aGGattack/remoter/project_plan/halo.drawio.png

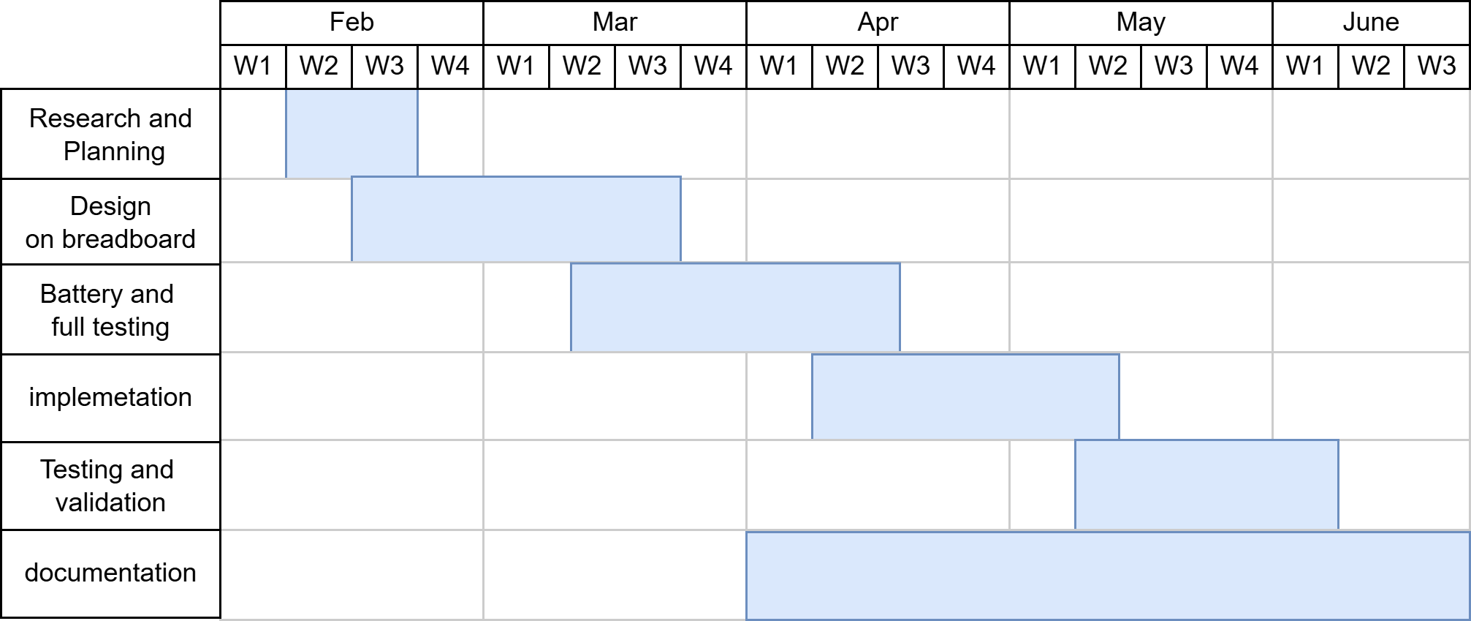
project_plan/halo.drawio.png
