aGGattack/remoter/project_plan/jaja.drawio.png

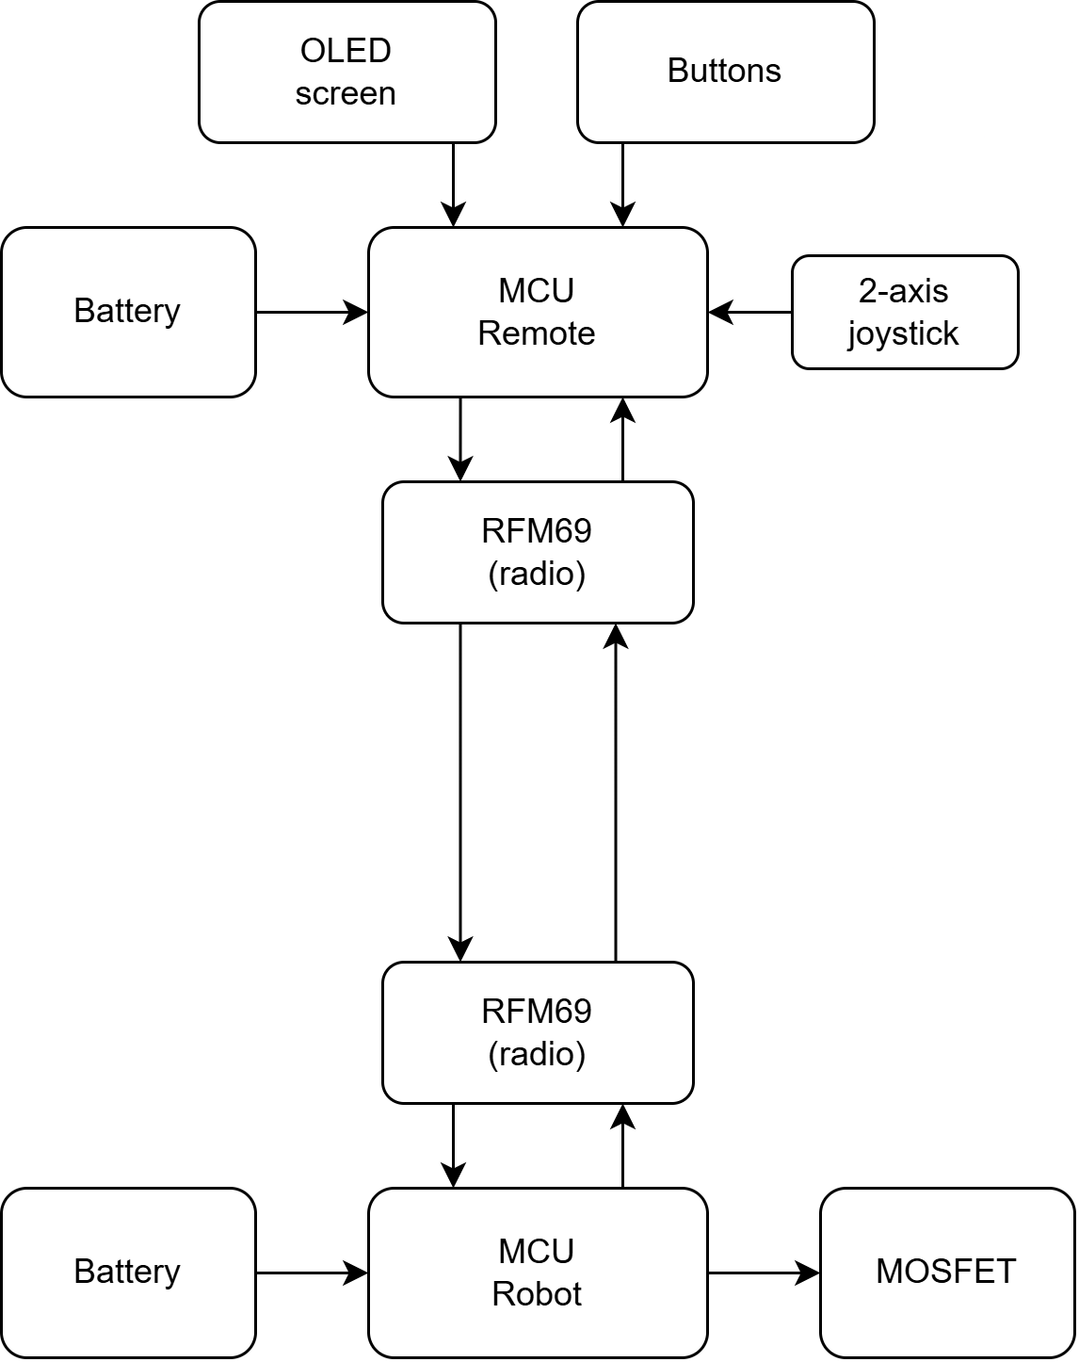
project_plan/jaja.drawio.png
