aGGattack/remoter/project_plan/komnu.drawio.png

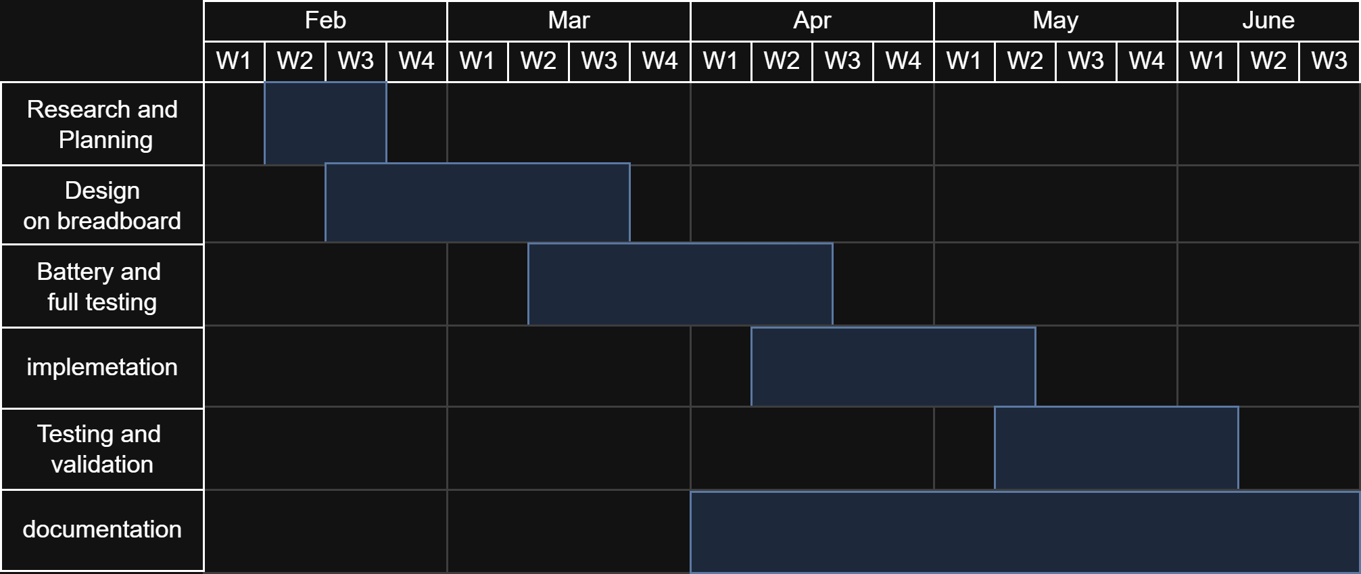
project_plan/komnu.drawio.png
