aGGattack/remoter/project_plan/yeps.drawio.png

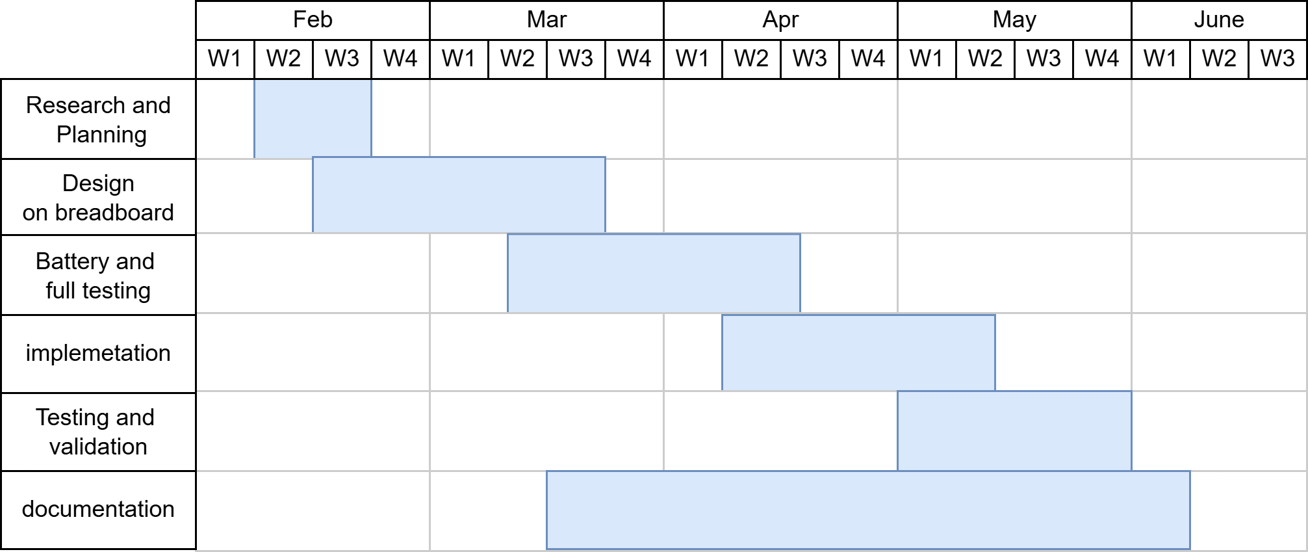
project_plan/yeps.drawio.png
