aGGattack/remoter/Project tests/Latency_Bitrate_PackageSize_Tests/packet_size_5B_9.6kb20260520_161618.png

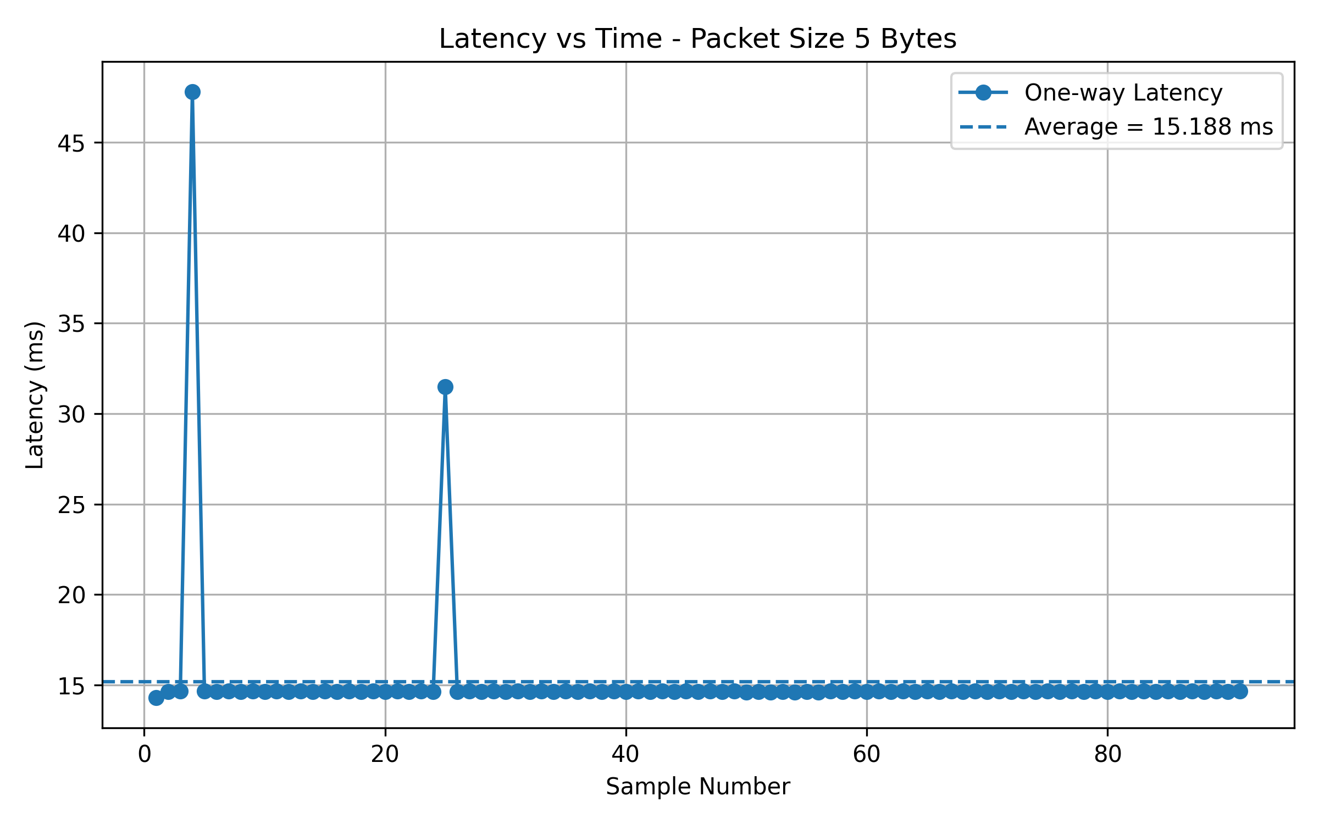
Project tests/Latency_Bitrate_PackageSize_Tests/packet_size_5B_9.6kb20260520_161618.png
