aGGattack/remoter/Project tests/Latency_Bitrate_PackageSize_Tests/packet_size_5B_57.6kb20260520_161243.png

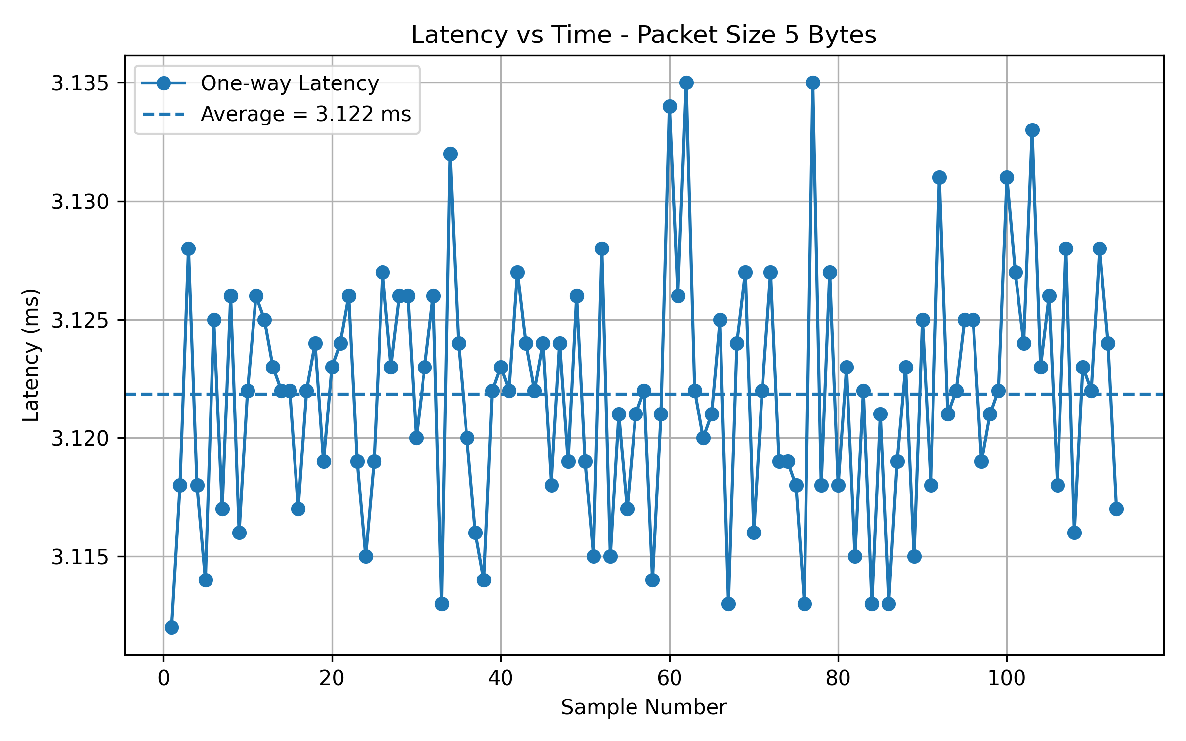
Project tests/Latency_Bitrate_PackageSize_Tests/packet_size_5B_57.6kb20260520_161243.png
