aGGattack/remoter/Project tests/Latency_Bitrate_PackageSize_Tests/packet_size_5B_115.2kb20260520_162811.png

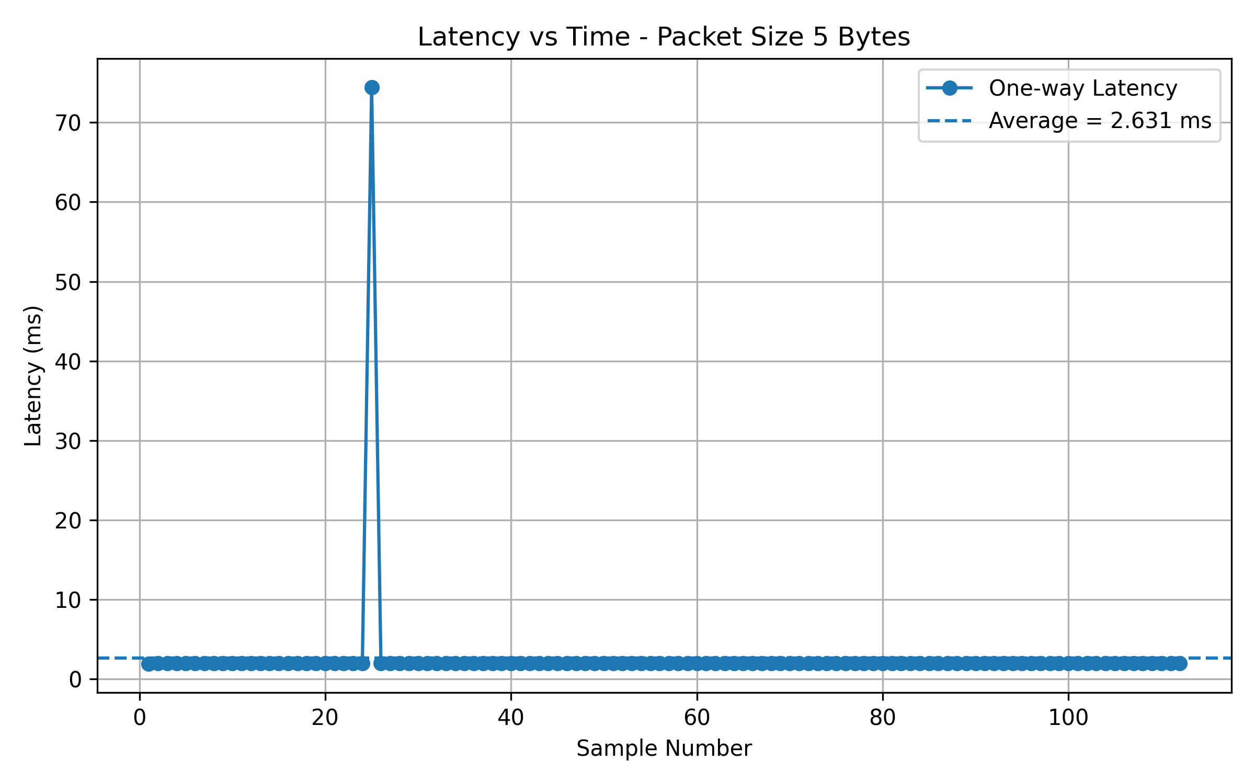
Project tests/Latency_Bitrate_PackageSize_Tests/packet_size_5B_115.2kb20260520_162811.png
