aGGattack/remoter/Project tests/Latency_Bitrate_PackageSize_Tests/packet_size_16B_9.6kb20260520_161730.png

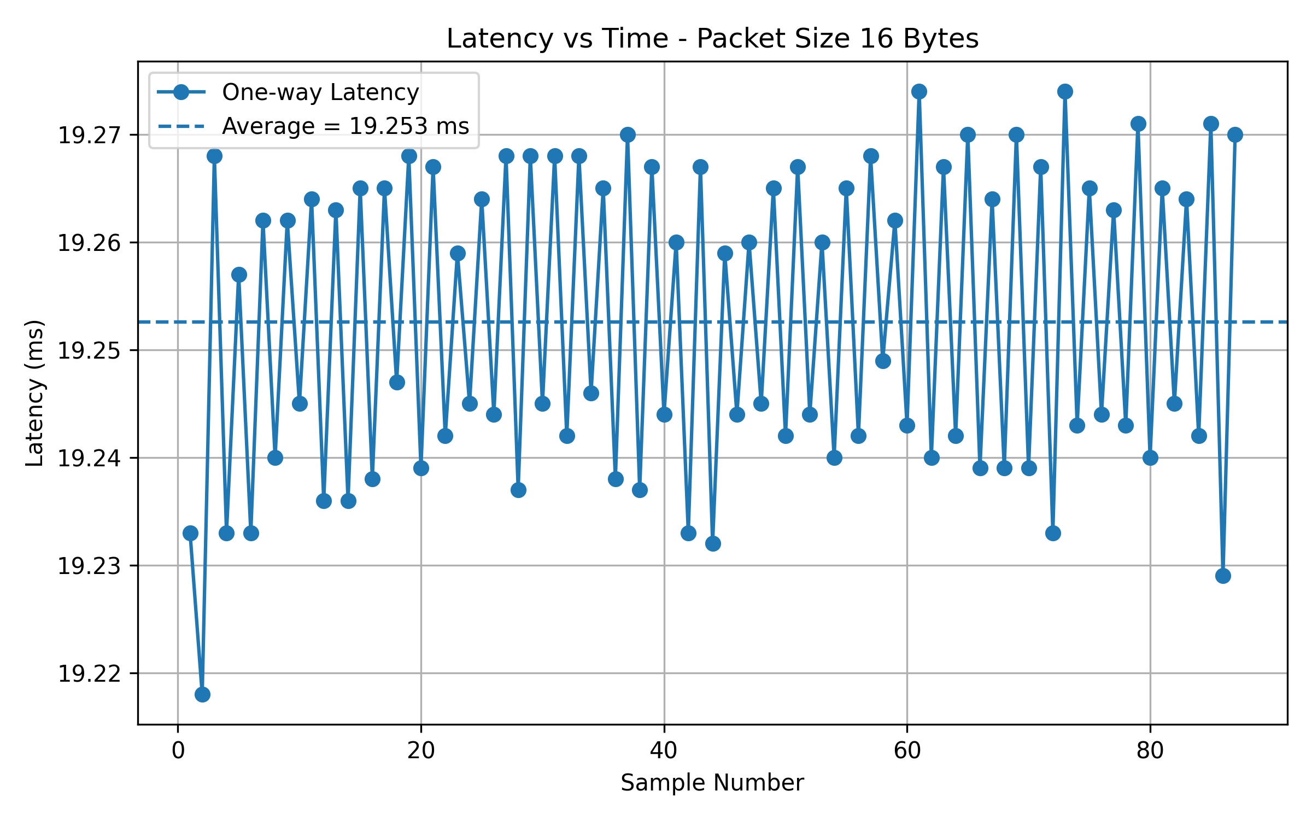
Project tests/Latency_Bitrate_PackageSize_Tests/packet_size_16B_9.6kb20260520_161730.png
