aGGattack/remoter/Project tests/Latency_Bitrate_PackageSize_Tests/packet_size_16B_57.6kb20260520_161135.png

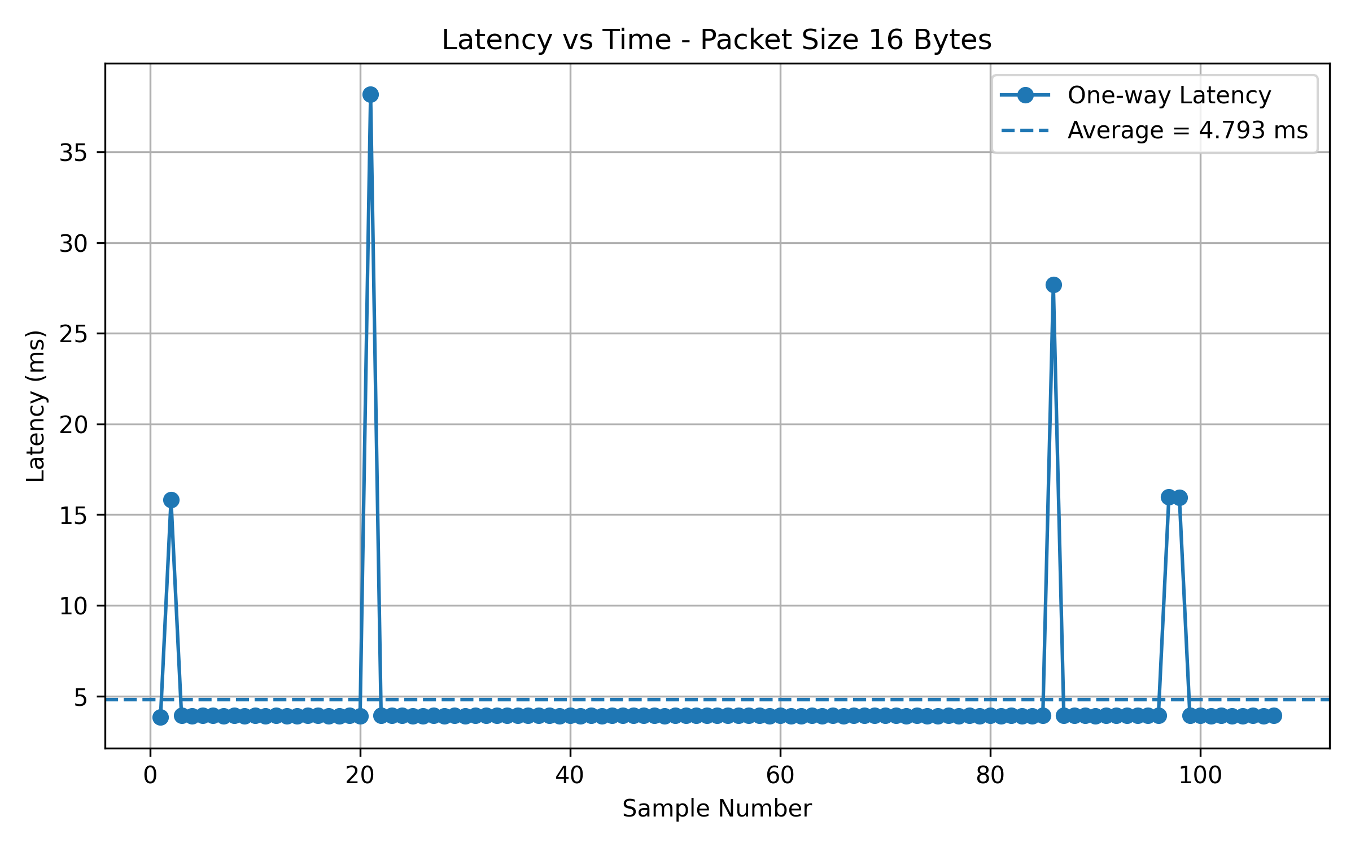
Project tests/Latency_Bitrate_PackageSize_Tests/packet_size_16B_57.6kb20260520_161135.png
