aGGattack/remoter/Project tests/Latency_Bitrate_PackageSize_Tests/packet_size_16B_115.2kb20260520_162728.png

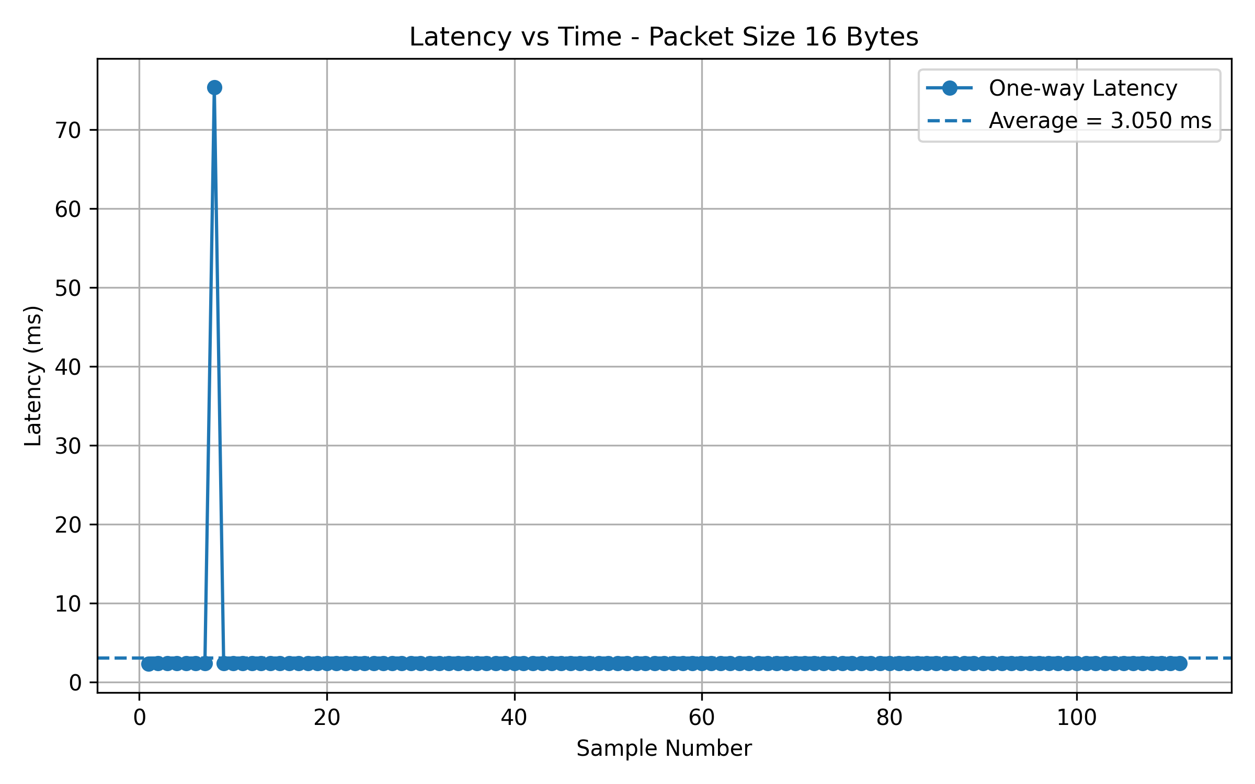
Project tests/Latency_Bitrate_PackageSize_Tests/packet_size_16B_115.2kb20260520_162728.png
