aGGattack/remoter/Project tests/Latency_Bitrate_PackageSize_Tests/packet_size_32B_9.6kb20260520_161826.png

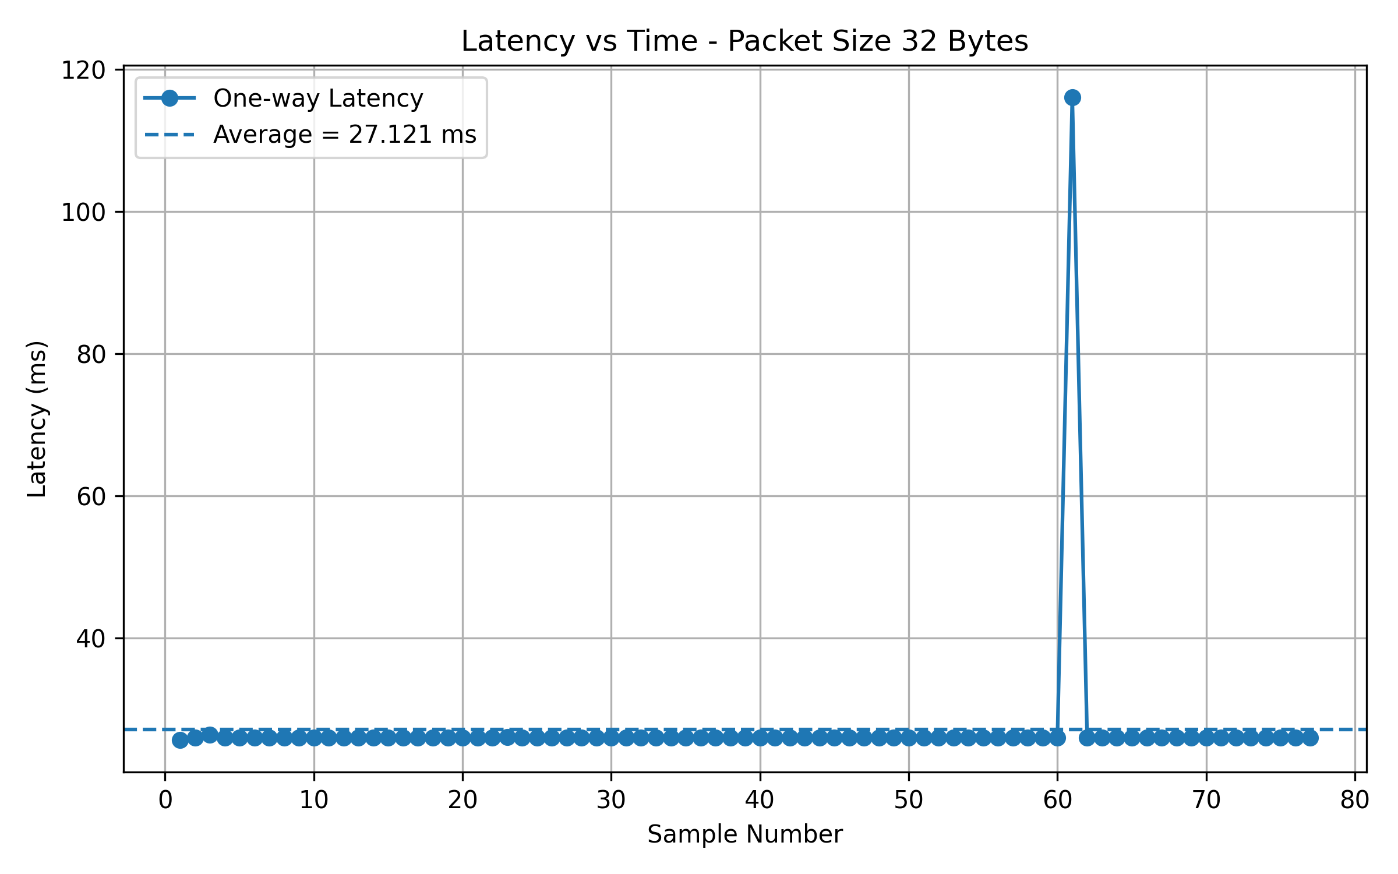
Project tests/Latency_Bitrate_PackageSize_Tests/packet_size_32B_9.6kb20260520_161826.png
