aGGattack/remoter/Project tests/Latency_Bitrate_PackageSize_Tests/packet_size_32B_57.6kb20260520_161049.png

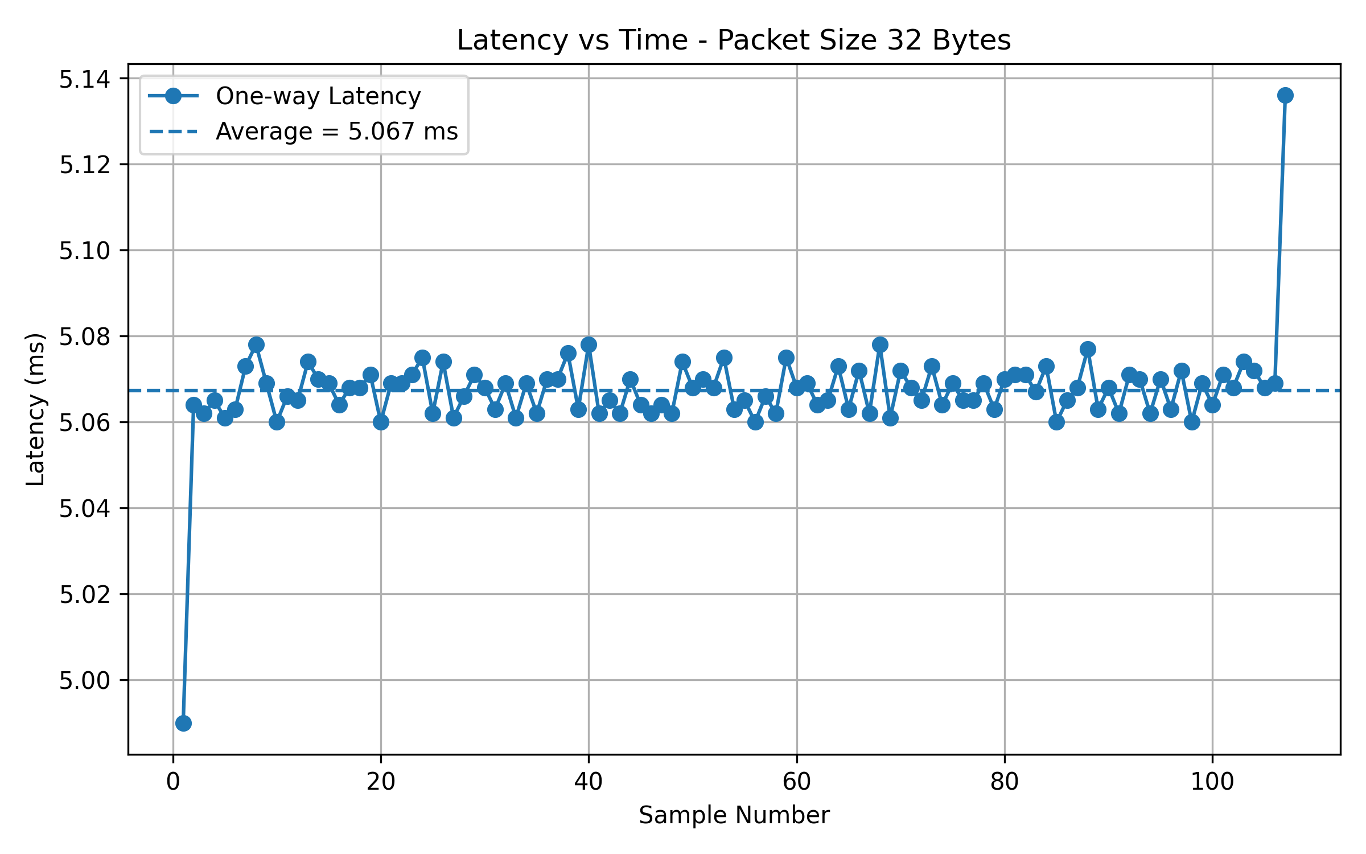
Project tests/Latency_Bitrate_PackageSize_Tests/packet_size_32B_57.6kb20260520_161049.png
