aGGattack/remoter/Project tests/Latency_Bitrate_PackageSize_Tests/packet_size_32B_115.2kb20260520_162636.png

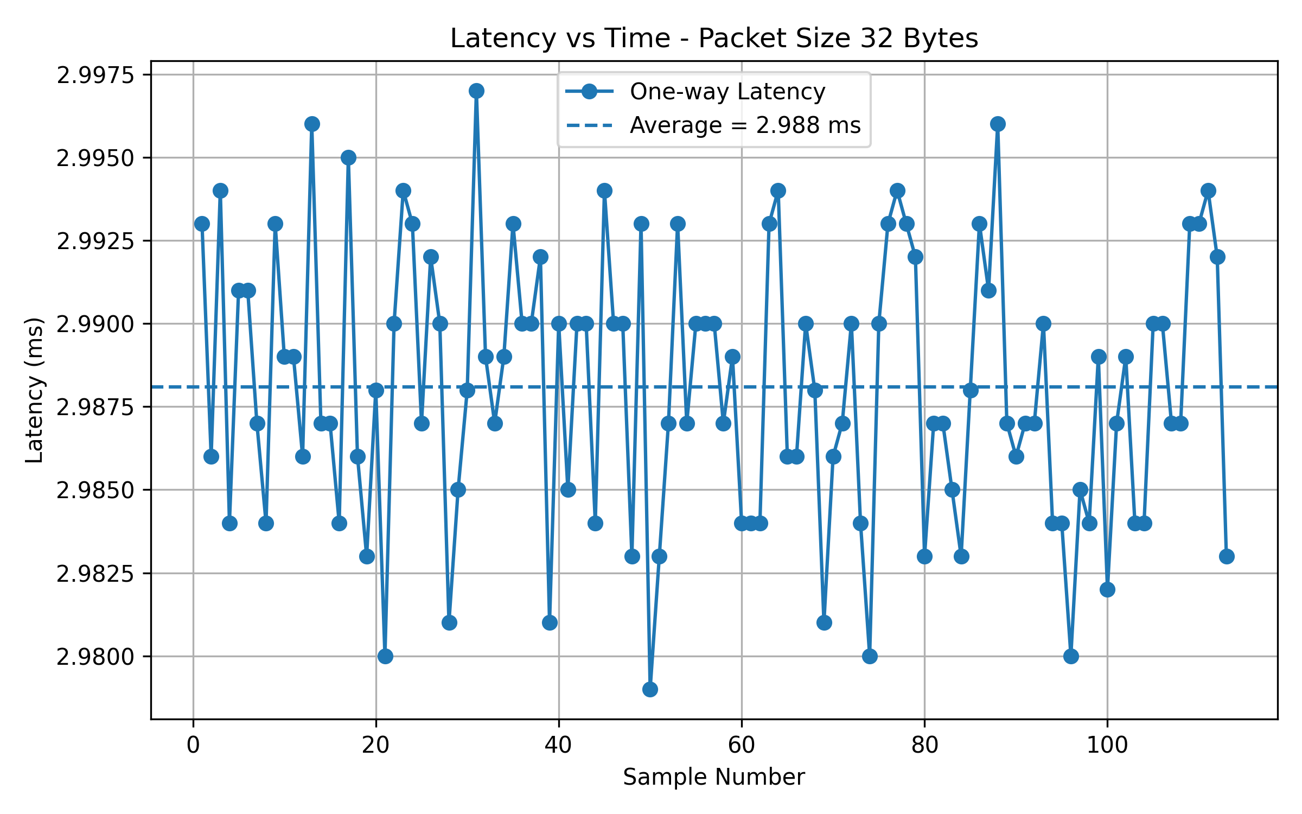
Project tests/Latency_Bitrate_PackageSize_Tests/packet_size_32B_115.2kb20260520_162636.png
