aGGattack/remoter/Project tests/Latency_Bitrate_PackageSize_Tests/packet_size_48B_9.6kb20260520_162034.png

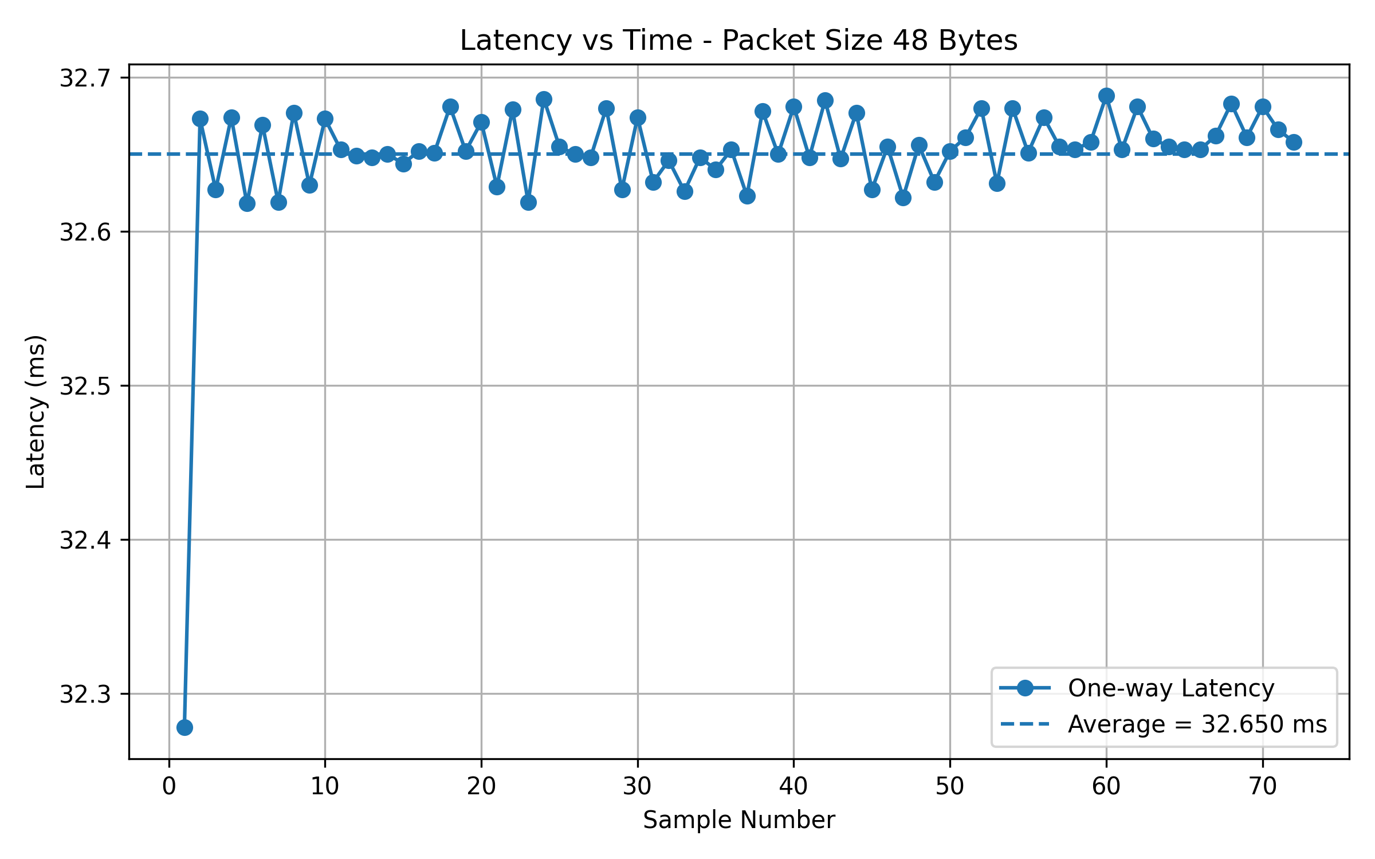
Project tests/Latency_Bitrate_PackageSize_Tests/packet_size_48B_9.6kb20260520_162034.png
