aGGattack/remoter/Project tests/Latency_Bitrate_PackageSize_Tests/packet_size_48B_57.6kb20260520_161003.png

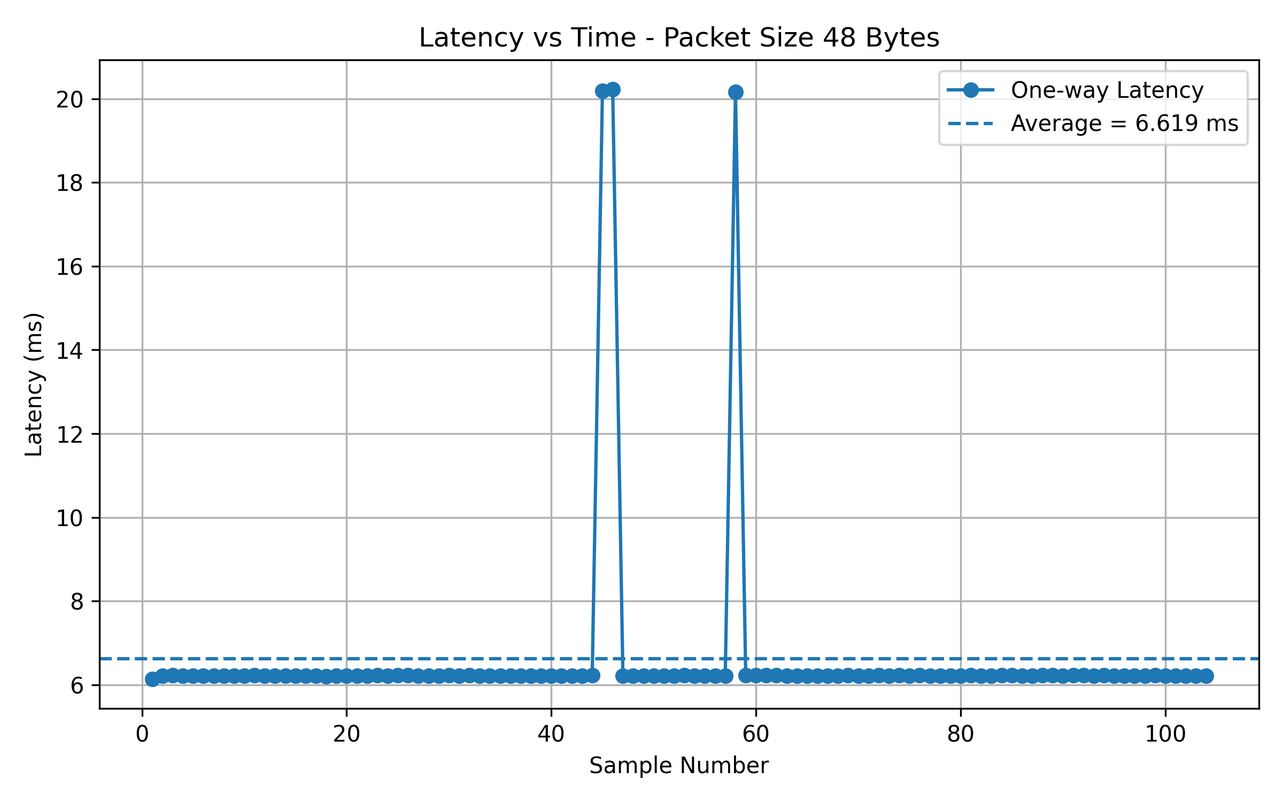
Project tests/Latency_Bitrate_PackageSize_Tests/packet_size_48B_57.6kb20260520_161003.png
