aGGattack/remoter/Project tests/Latency_Bitrate_PackageSize_Tests/packet_size_48B_115.2kb20260520_162426.png

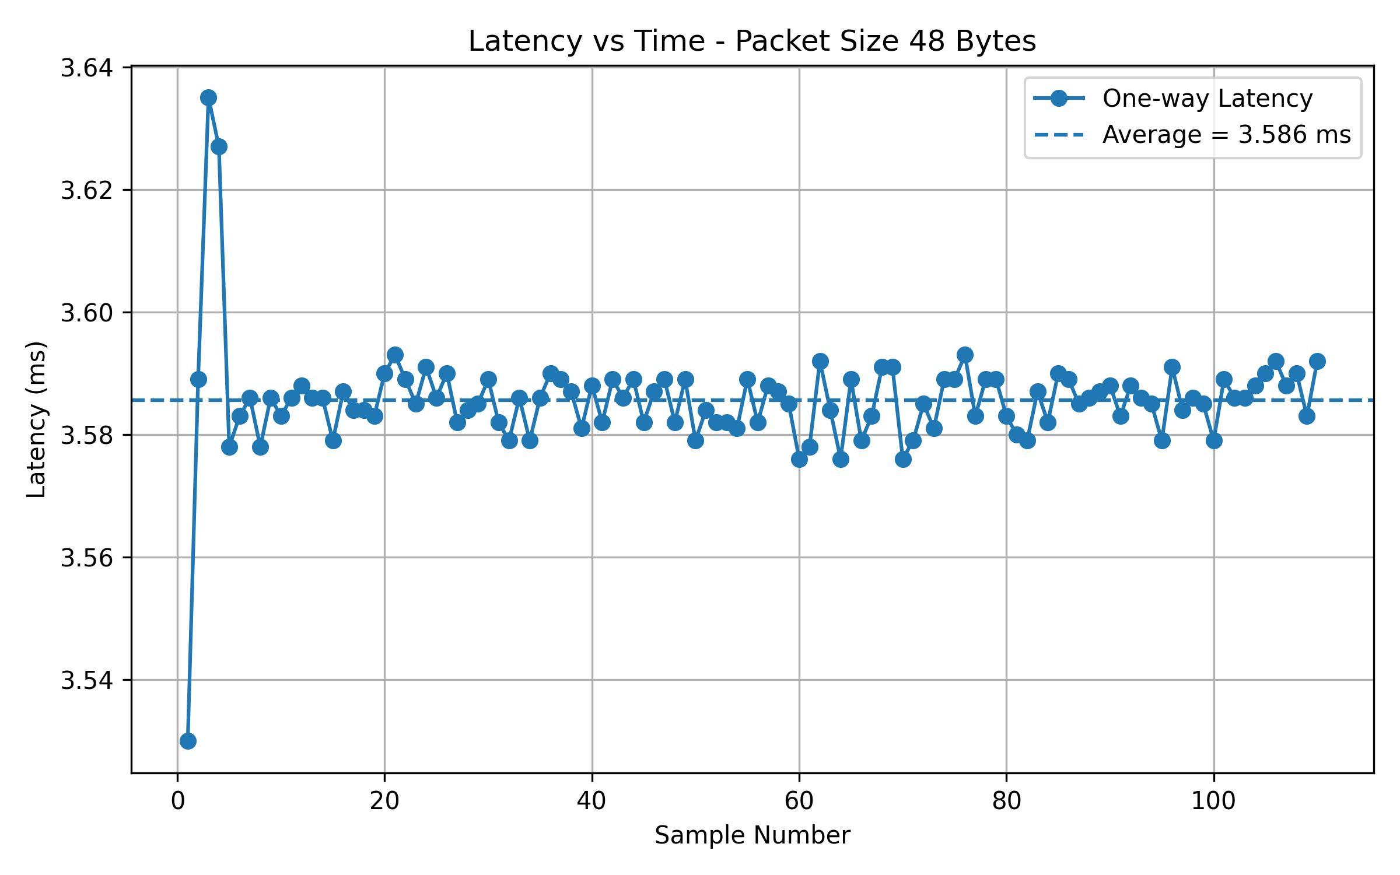
Project tests/Latency_Bitrate_PackageSize_Tests/packet_size_48B_115.2kb20260520_162426.png
