aGGattack/remoter/Project tests/Latency_Bitrate_PackageSize_Tests/packet_size_64B_9.6kb20260520_162110.png

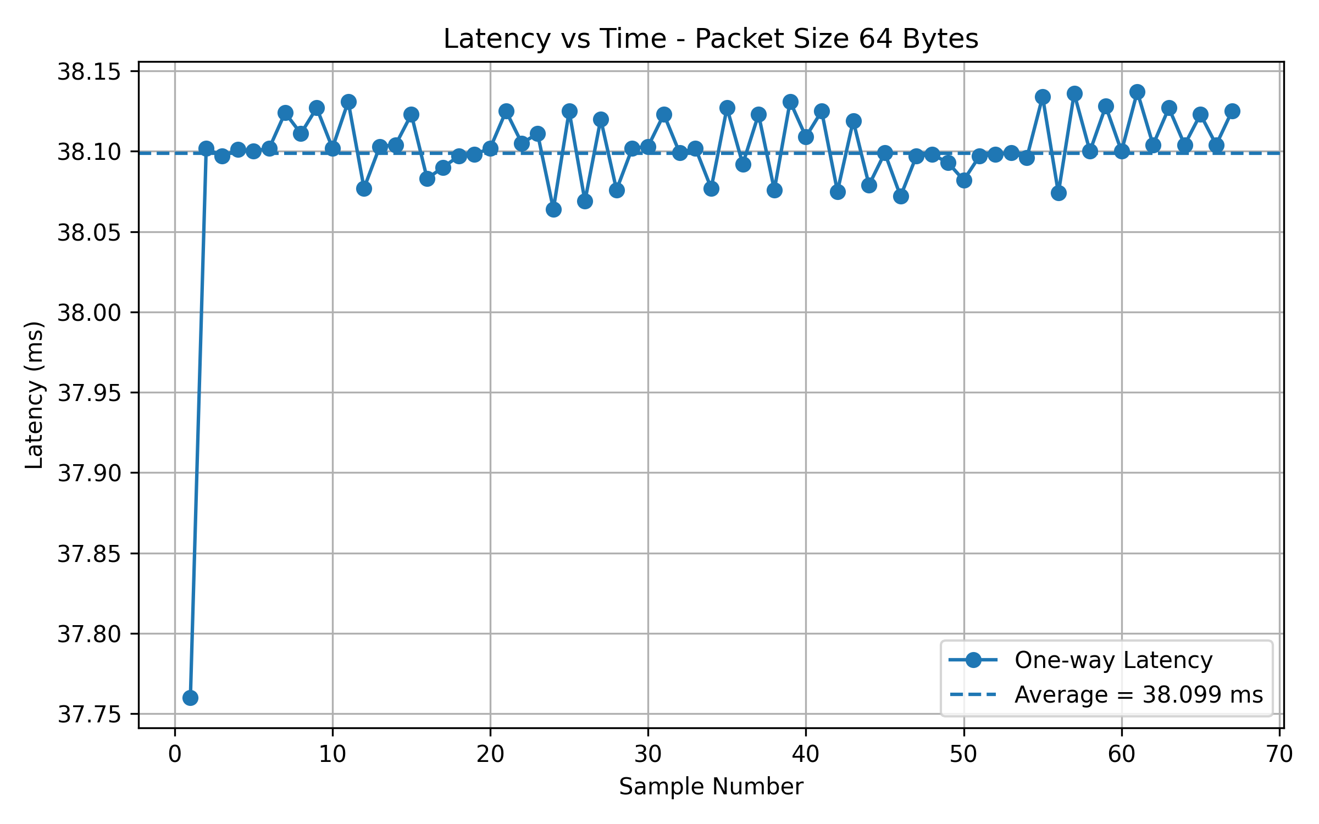
Project tests/Latency_Bitrate_PackageSize_Tests/packet_size_64B_9.6kb20260520_162110.png
