aGGattack/remoter/Project tests/Latency_Bitrate_PackageSize_Tests/plot_boxplot_rtt.png

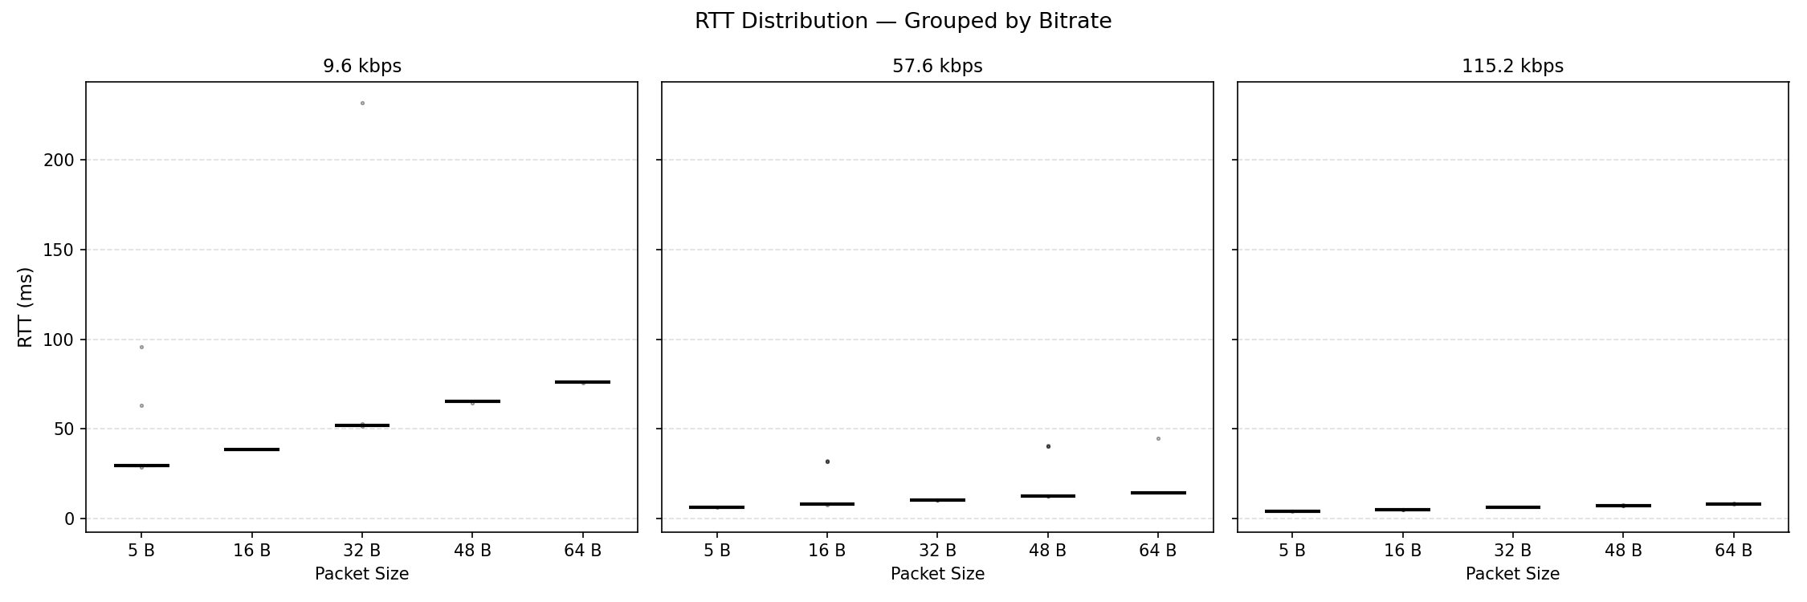
Project tests/Latency_Bitrate_PackageSize_Tests/plot_boxplot_rtt.png
