aGGattack/remoter/Project tests/Latency_Bitrate_PackageSize_Tests/plot_grouped_bar.png

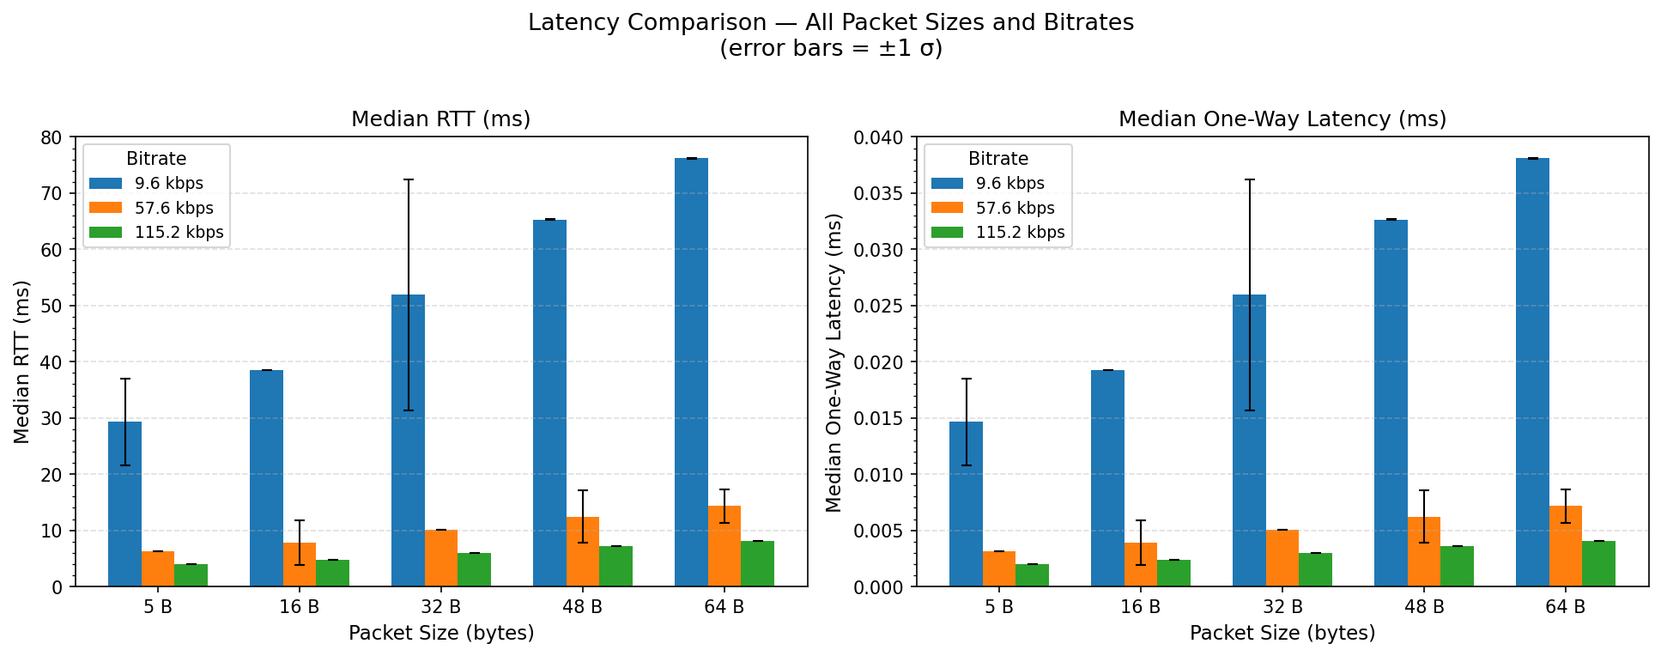
Project tests/Latency_Bitrate_PackageSize_Tests/plot_grouped_bar.png
