aGGattack/remoter/Project tests/Latency_Bitrate_PackageSize_Tests/plot_heatmap_owl.png

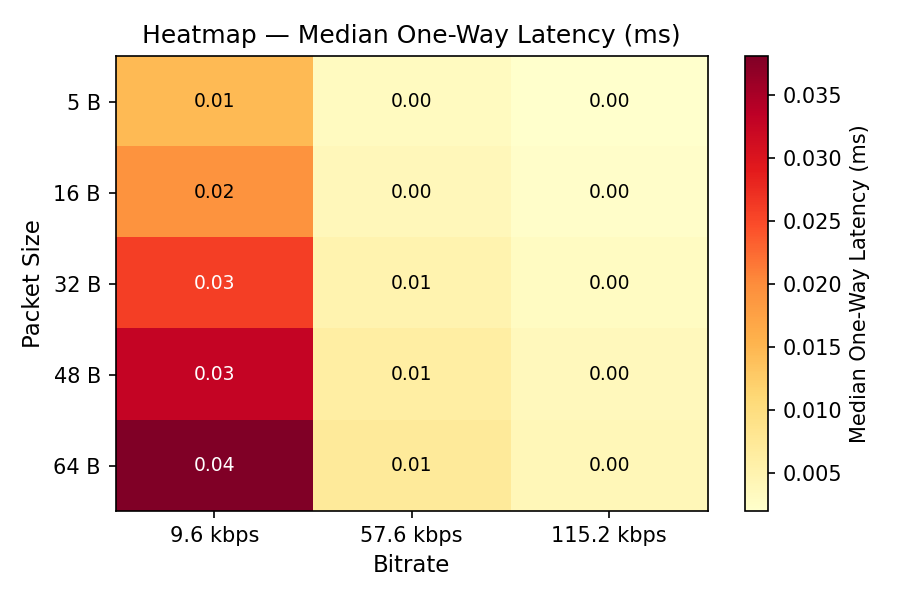
Project tests/Latency_Bitrate_PackageSize_Tests/plot_heatmap_owl.png
