aGGattack/remoter/Project tests/Latency_Bitrate_PackageSize_Tests/plot_owl_vs_packet_size.png

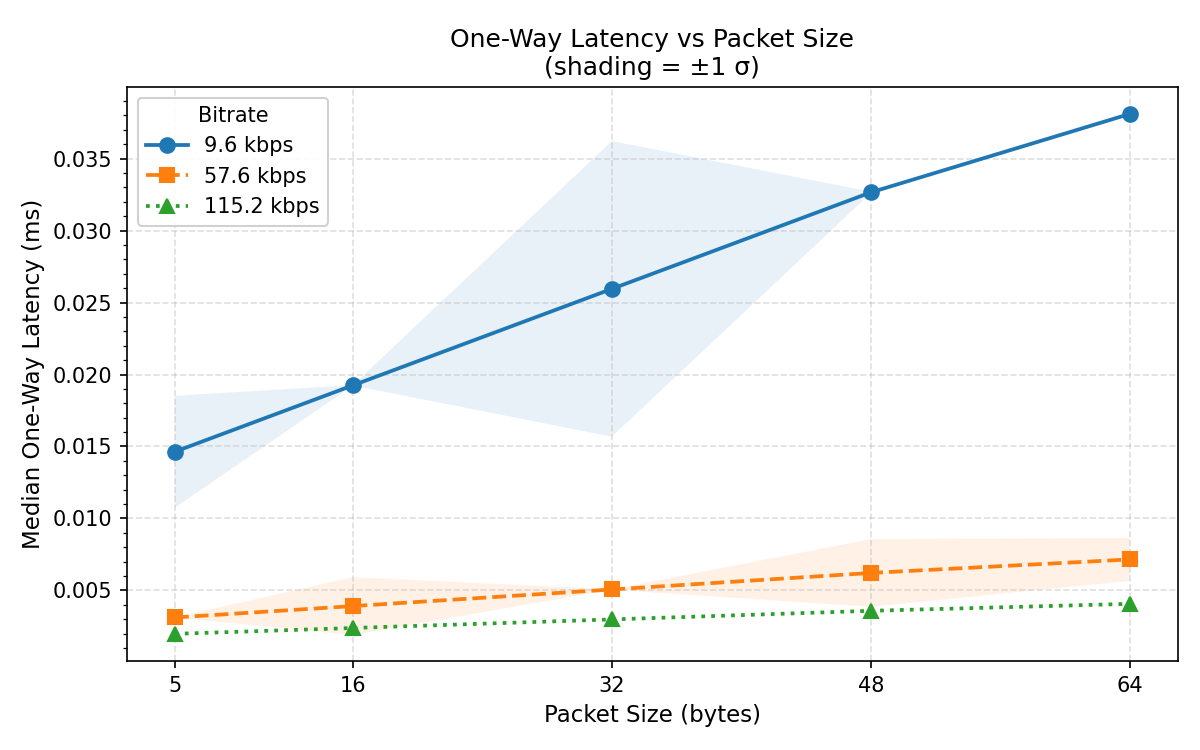
Project tests/Latency_Bitrate_PackageSize_Tests/plot_owl_vs_packet_size.png
