aGGattack/remoter/Project tests/latency_Bitrate_test/latency_1.2_kbps_20260520_152502.png

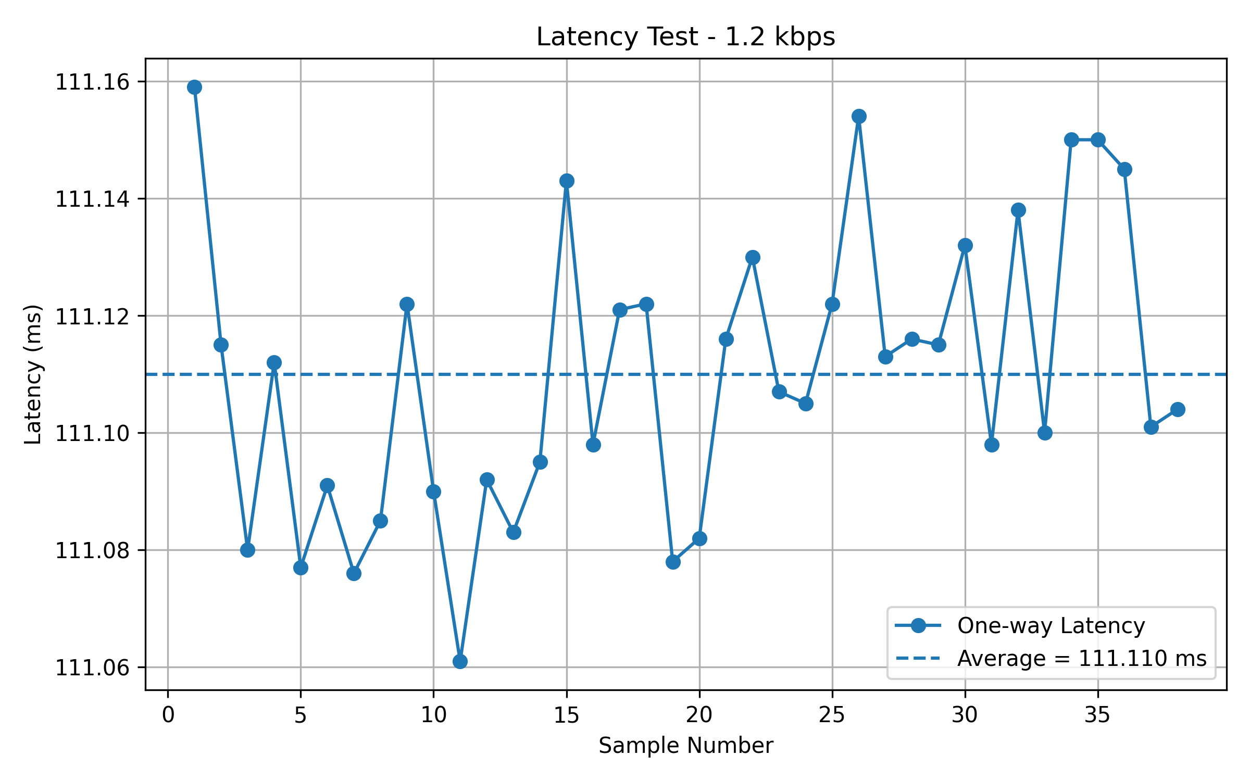
Project tests/latency_Bitrate_test/latency_1.2_kbps_20260520_152502.png
