aGGattack/remoter/Project tests/latency_Bitrate_test/latency_9.6_kbps_20260520_150811.png

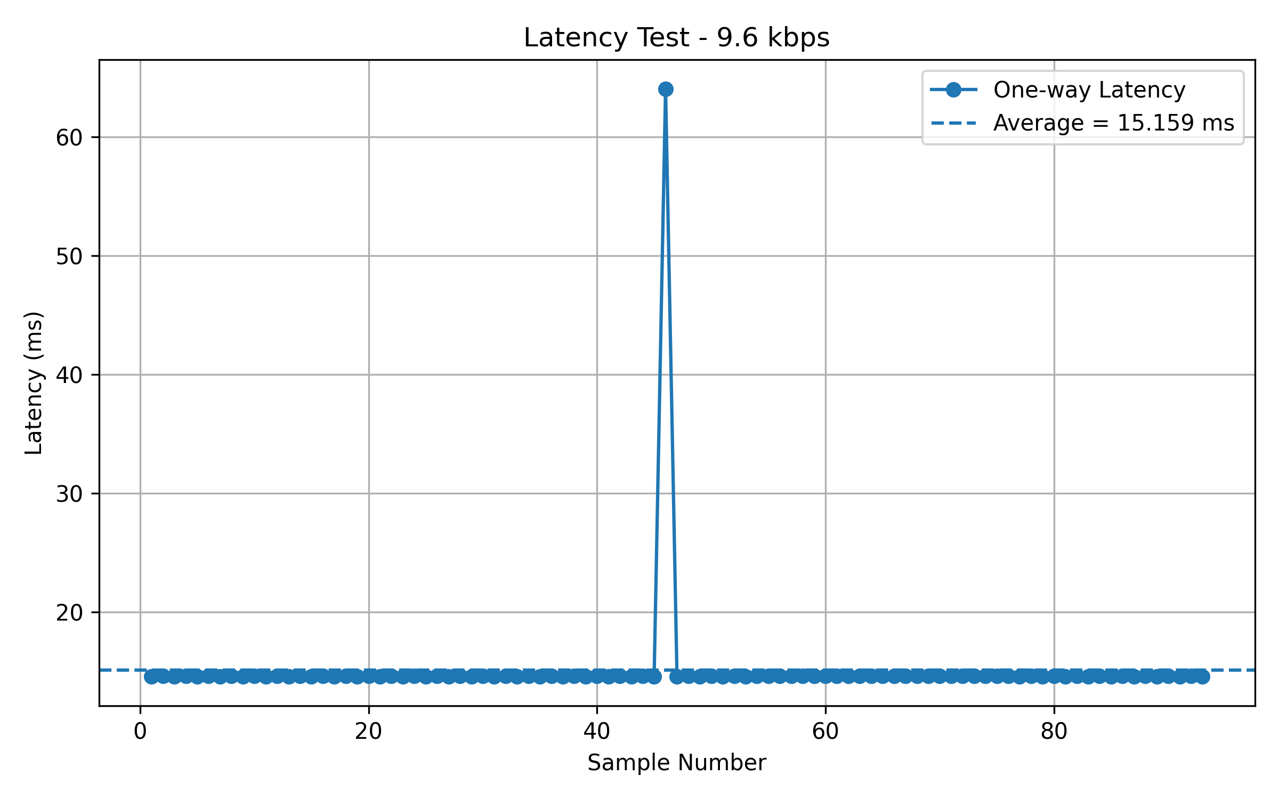
Project tests/latency_Bitrate_test/latency_9.6_kbps_20260520_150811.png
