aGGattack/remoter/Project tests/latency_Bitrate_test/latency_57.6_kbps_20260520_150318.png

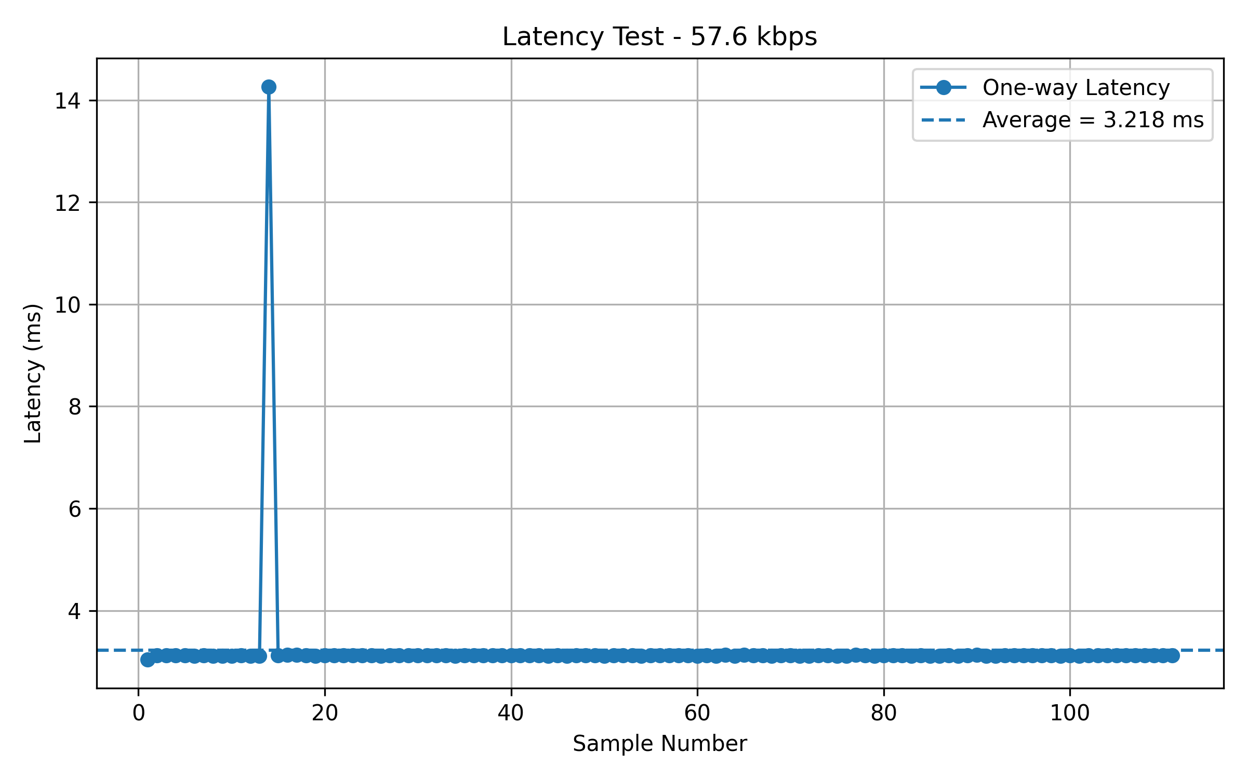
Project tests/latency_Bitrate_test/latency_57.6_kbps_20260520_150318.png
