aGGattack/remoter/Project tests/latency_Bitrate_test/latency_115.2_kbps_20260520_150950.png

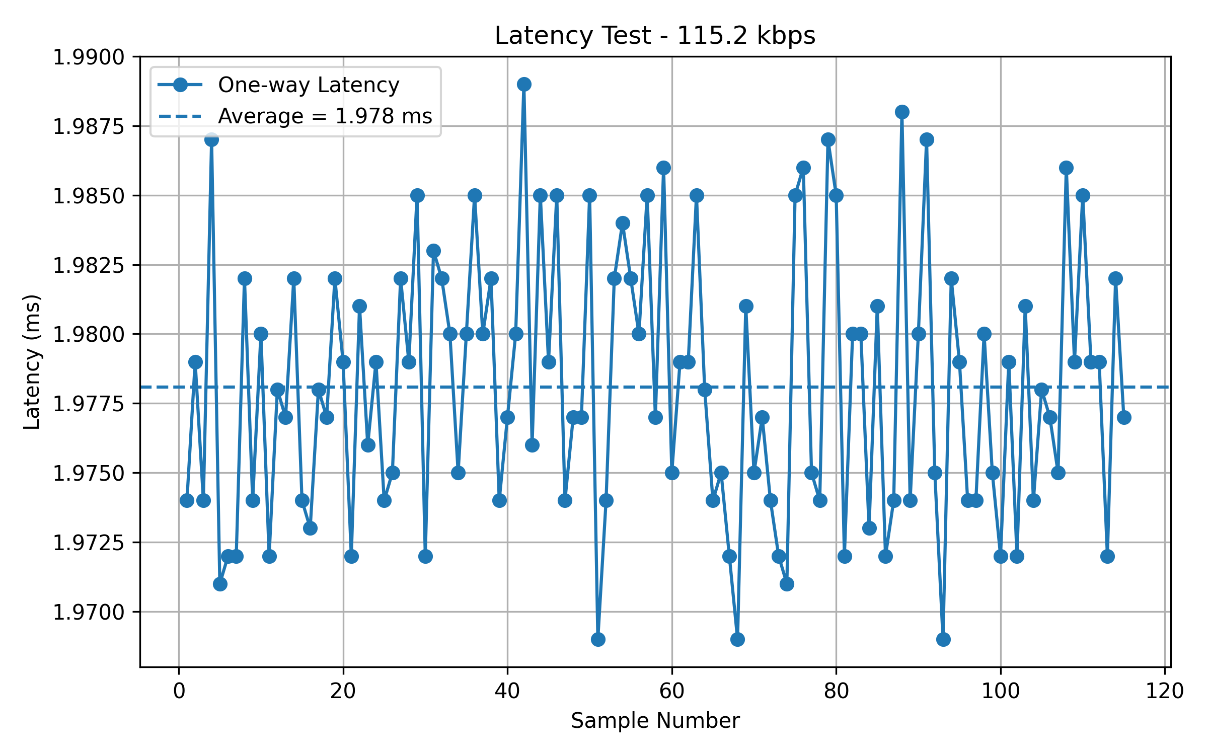
Project tests/latency_Bitrate_test/latency_115.2_kbps_20260520_150950.png
