aGGattack/remoter/Project tests/latency_Bitrate_test/latency_250_kbps_20260520_151310.png

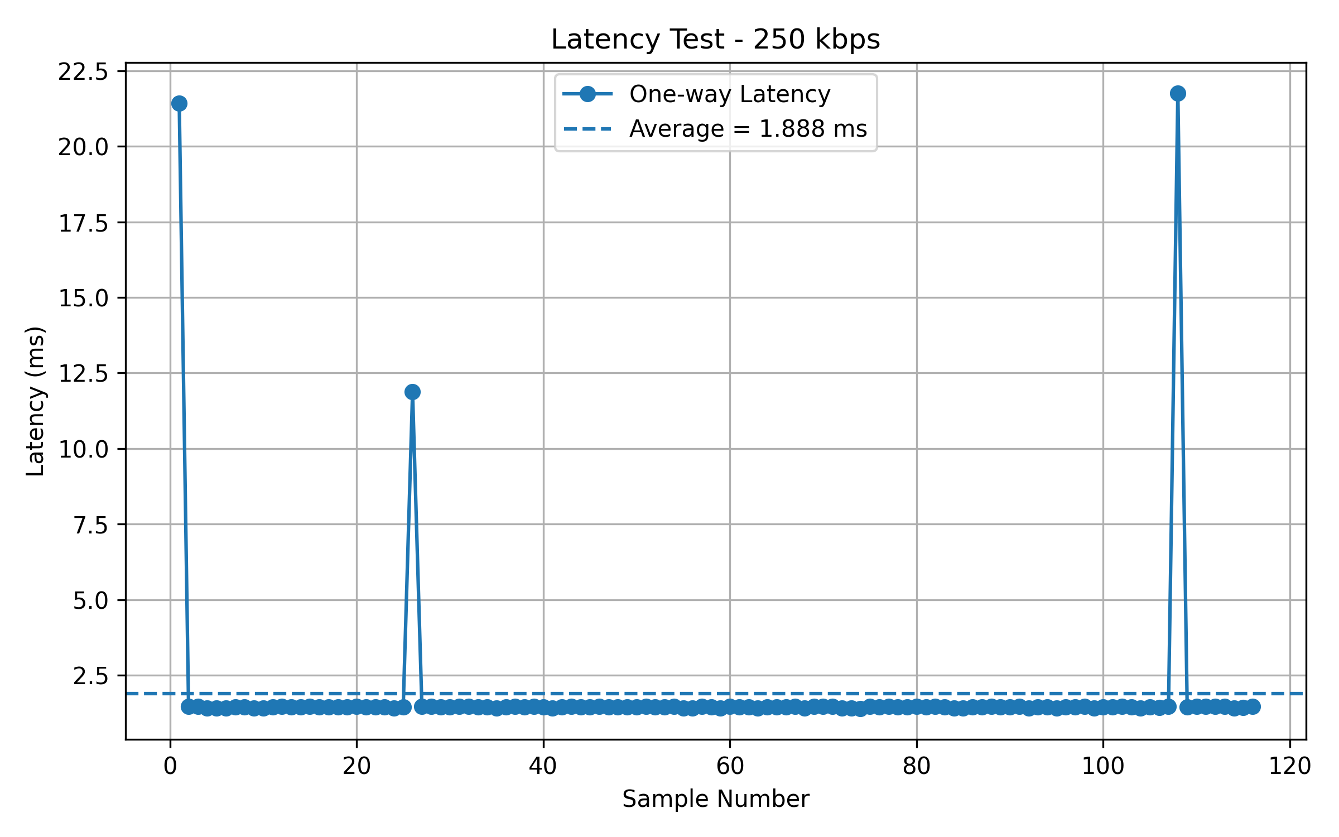
Project tests/latency_Bitrate_test/latency_250_kbps_20260520_151310.png
