aGGattack/remoter/Project tests/latency_Bitrate_test/plot_bar_rtt_owl.png

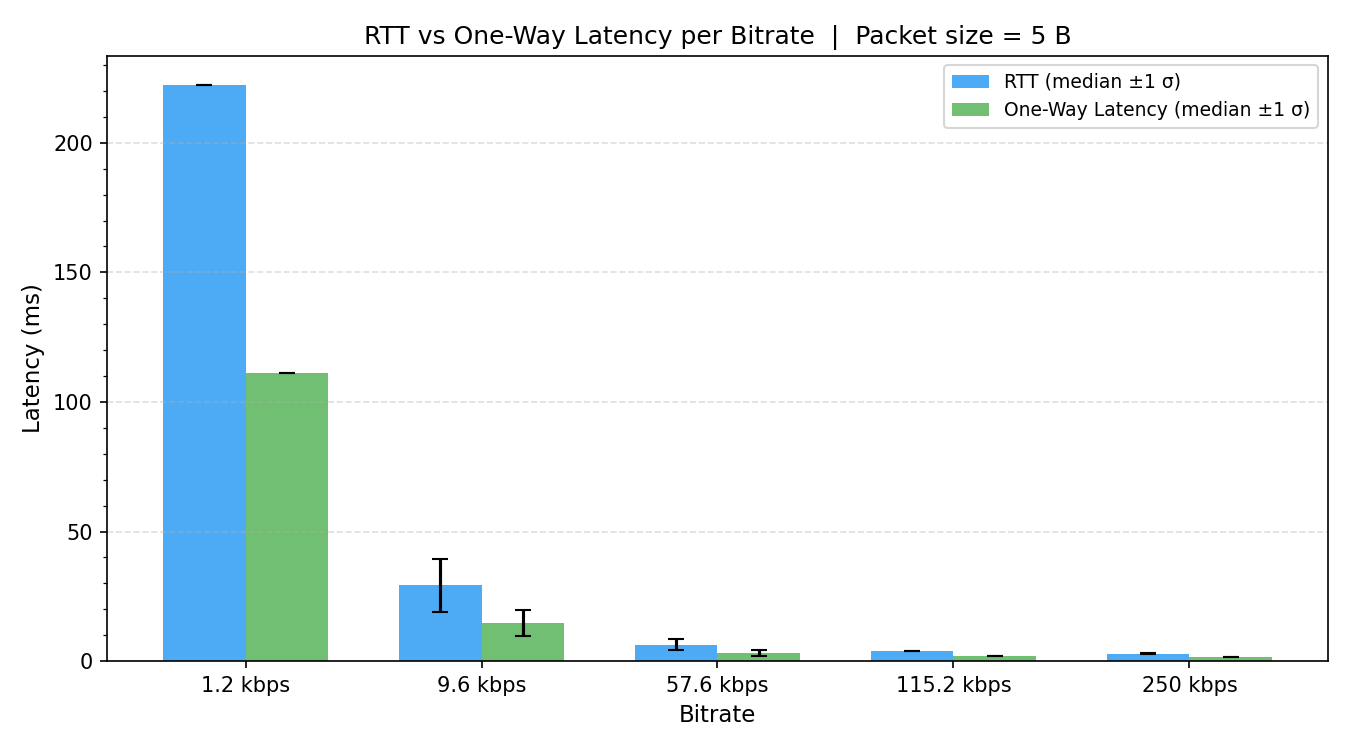
Project tests/latency_Bitrate_test/plot_bar_rtt_owl.png
