aGGattack/remoter/Project tests/latency_Bitrate_test/plot_boxplot_bitrate.png

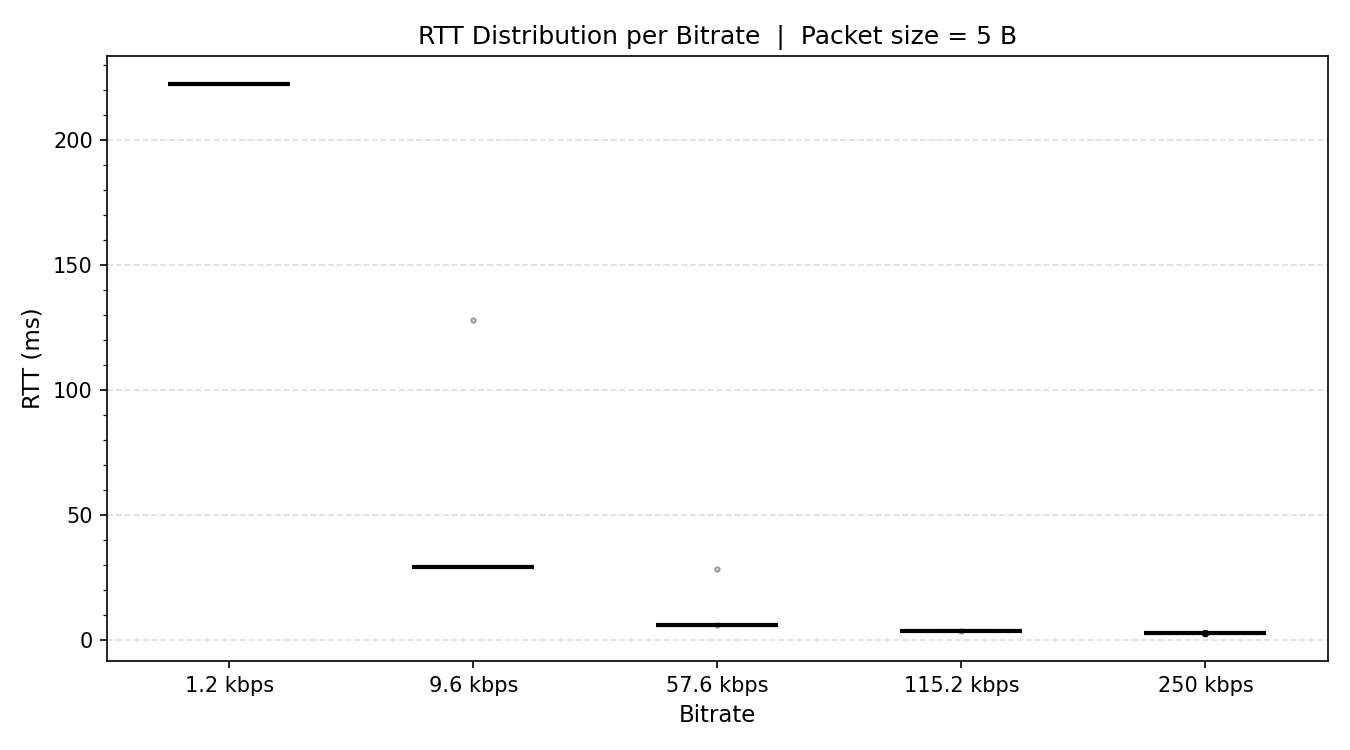
Project tests/latency_Bitrate_test/plot_boxplot_bitrate.png
