aGGattack/remoter/Project tests/latency_Bitrate_test/plot_rtt_vs_bitrate.png

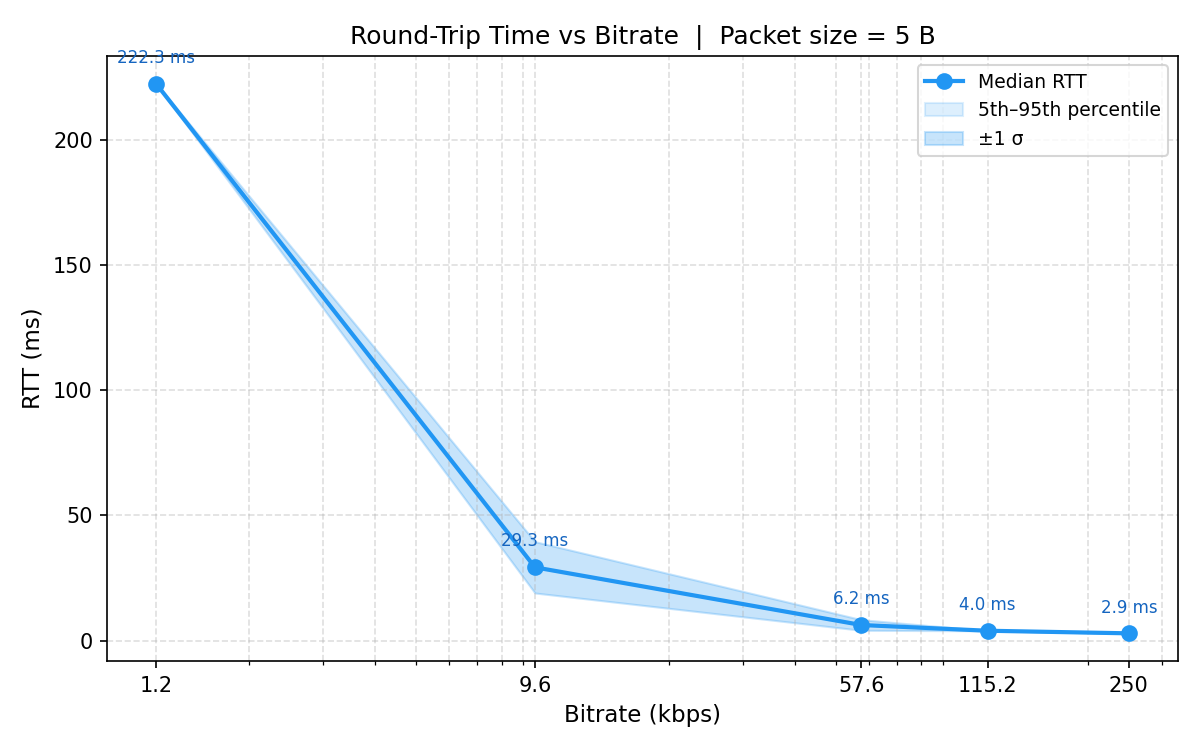
Project tests/latency_Bitrate_test/plot_rtt_vs_bitrate.png
