aGGattack/remoter/Project tests/RSSI_Antenna_test/plot_rssi_bar_per_distance.png

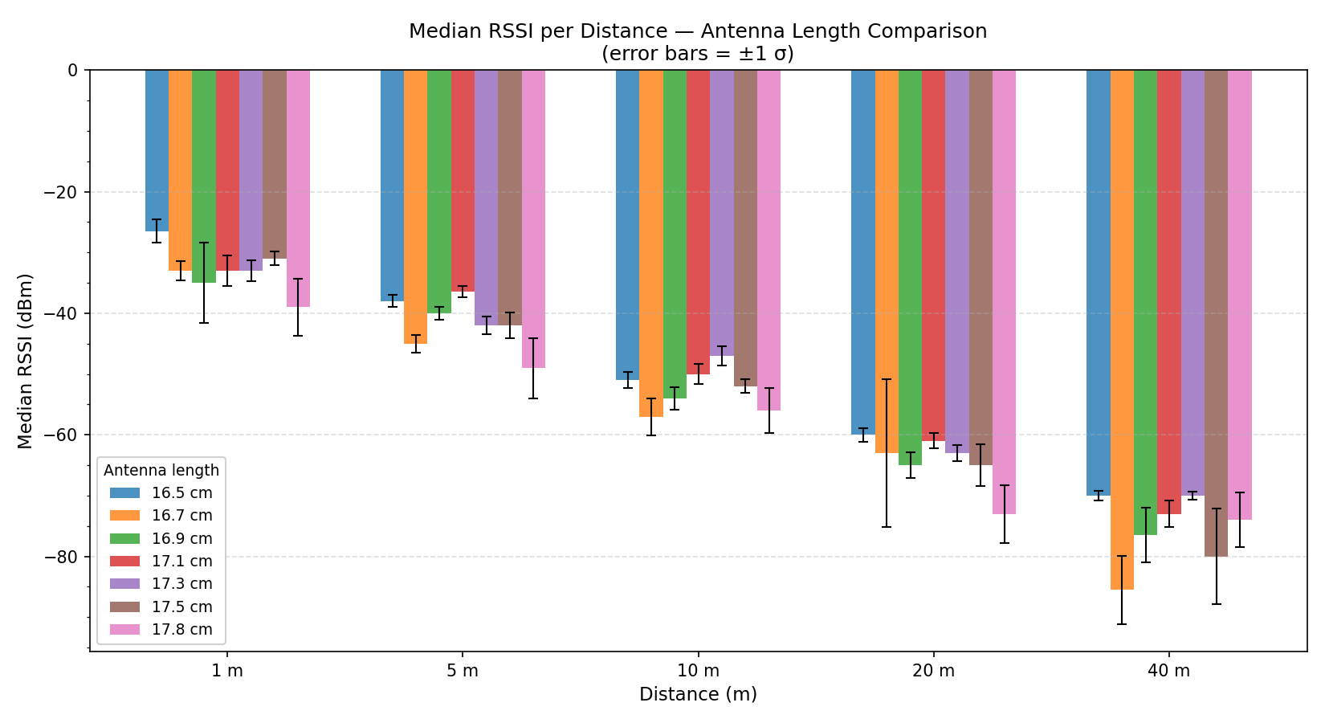
Project tests/RSSI_Antenna_test/plot_rssi_bar_per_distance.png
