aGGattack/remoter/Project tests/RSSI_Antenna_test/plot_rssi_boxplot_40m.png

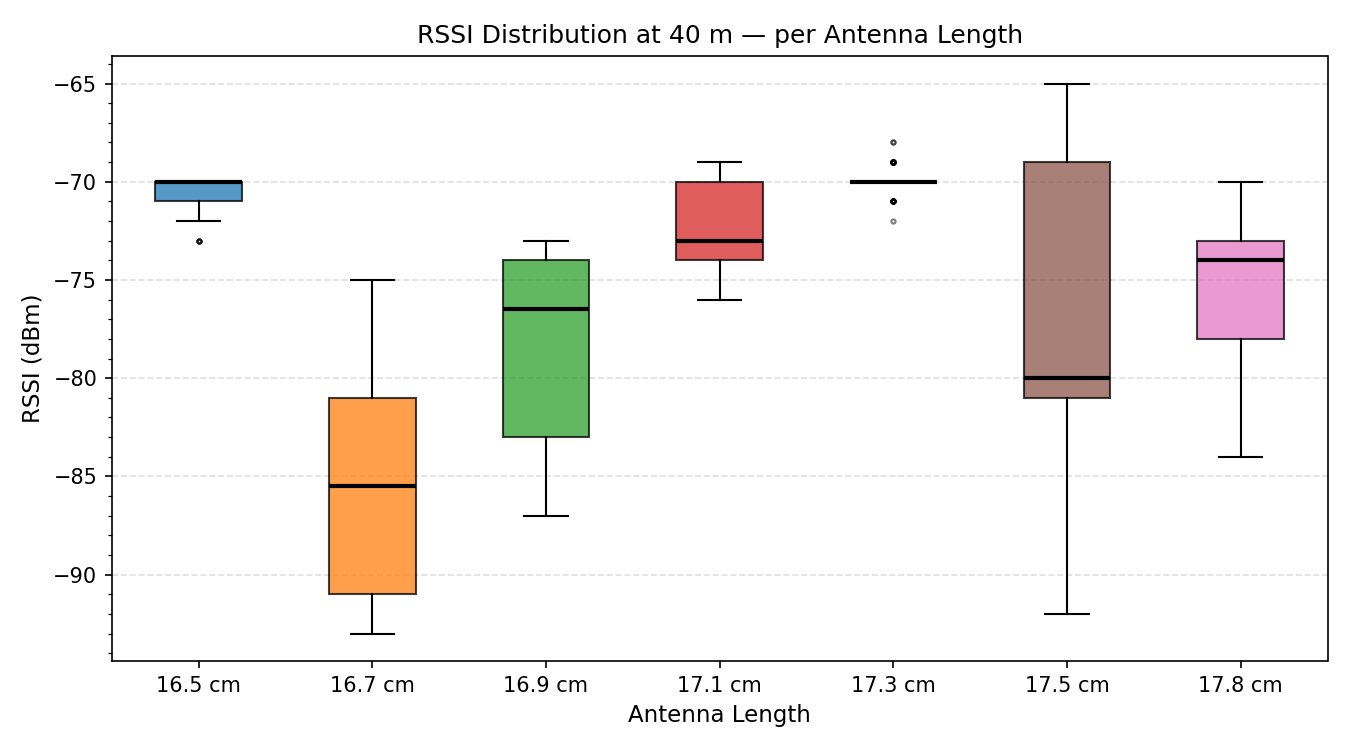
Project tests/RSSI_Antenna_test/plot_rssi_boxplot_40m.png
