aGGattack/remoter/Project tests/RSSI_Antenna_test/plot_rssi_vs_distance.png

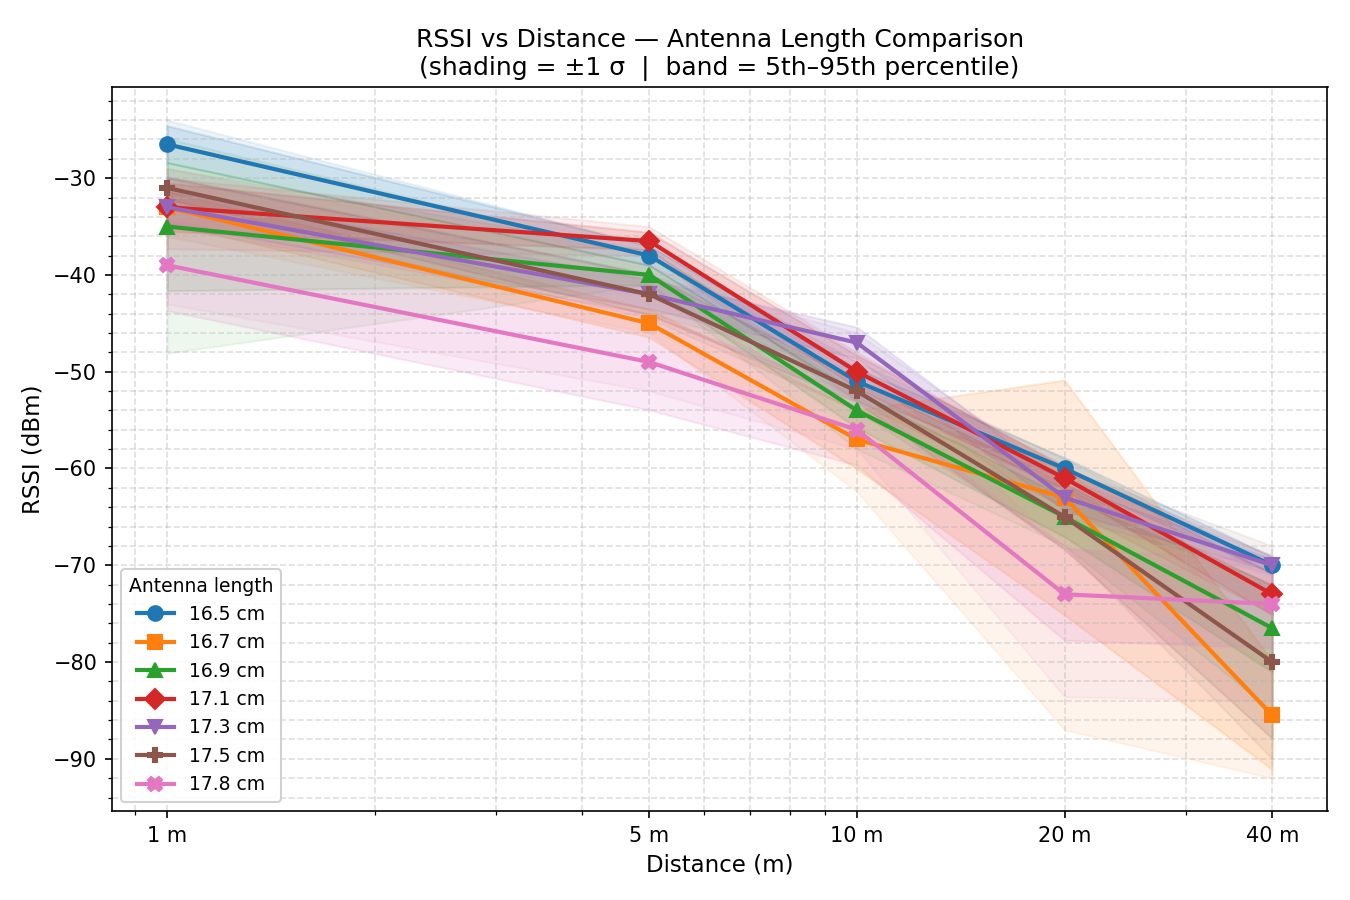
Project tests/RSSI_Antenna_test/plot_rssi_vs_distance.png
