aGGattack/remoter/Project tests/RSSI_Antenna_test/rssi_plot_Horizontal_16.5cm_20260521_145443.png

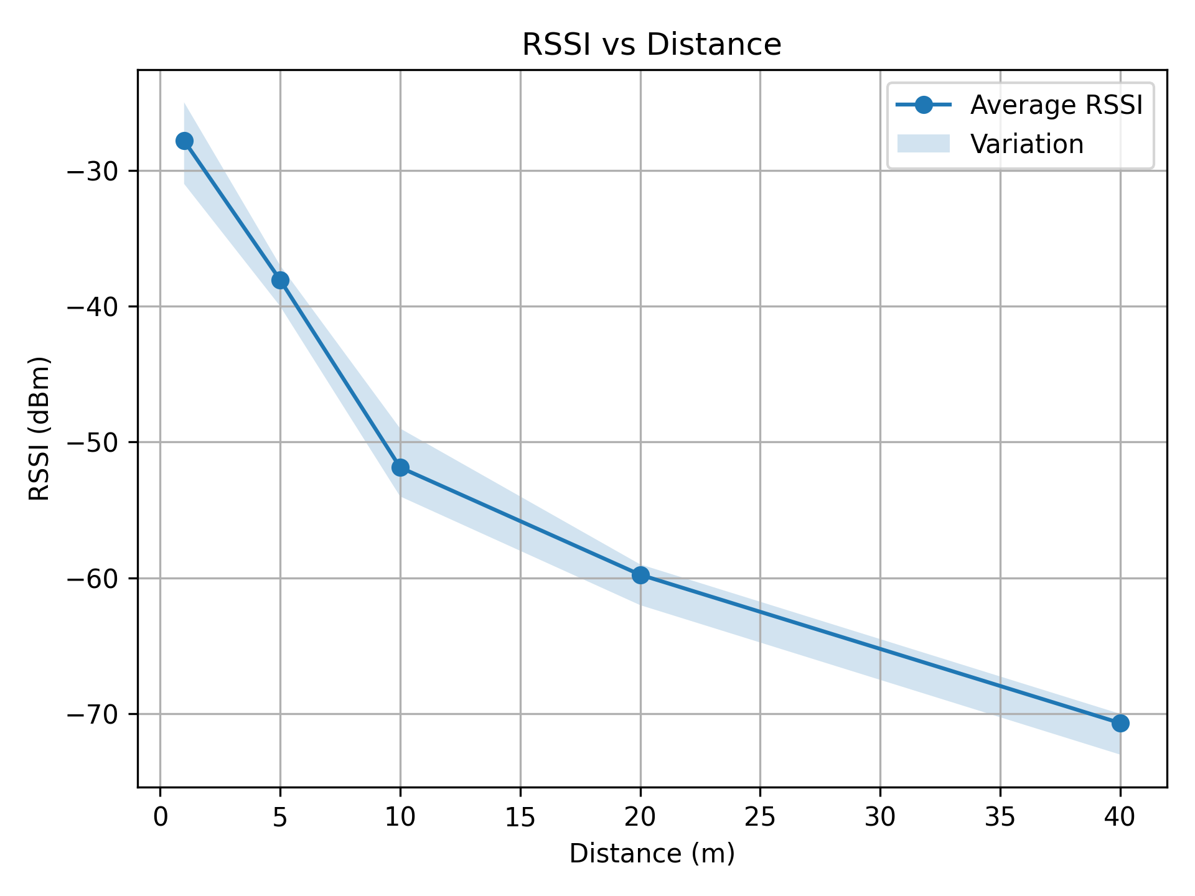
Project tests/RSSI_Antenna_test/rssi_plot_Horizontal_16.5cm_20260521_145443.png
