aGGattack/remoter/Project tests/RSSI_Antenna_test/rssi_plot_Horizontal_16.7cm_20260521_125546.png

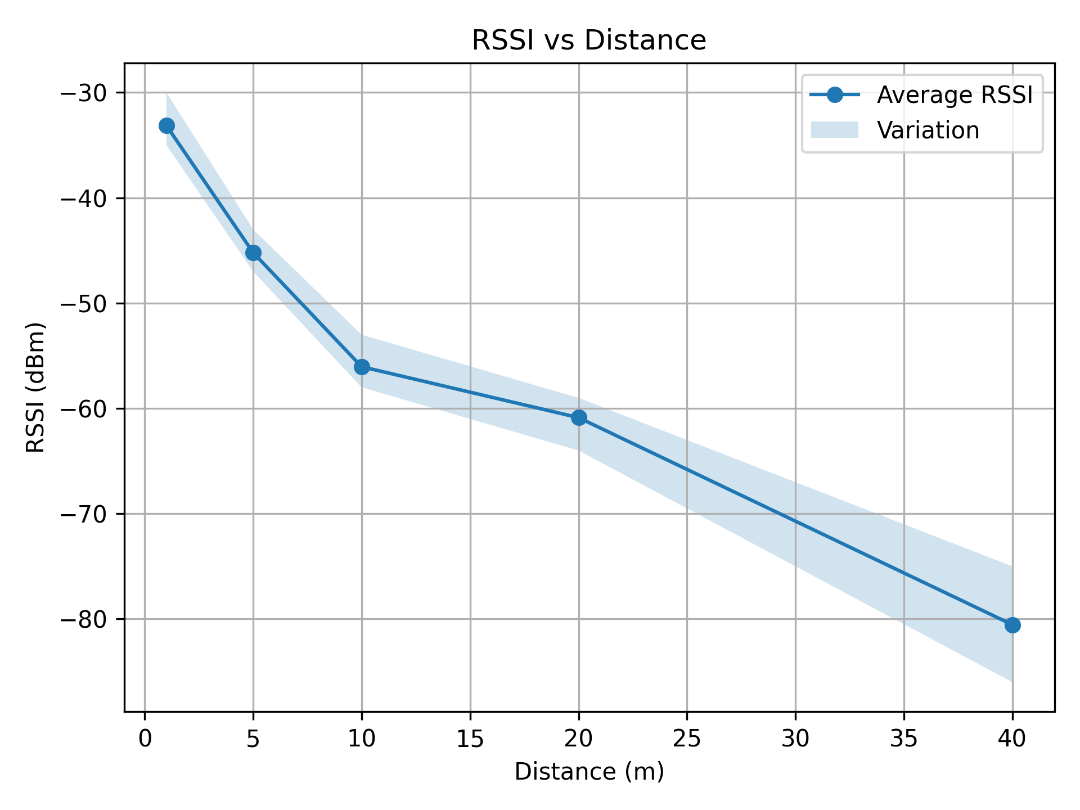
Project tests/RSSI_Antenna_test/rssi_plot_Horizontal_16.7cm_20260521_125546.png
