aGGattack/remoter/Project tests/RSSI_Antenna_test/rssi_plot_Horizontal_16.9cm_20260521_124703.png

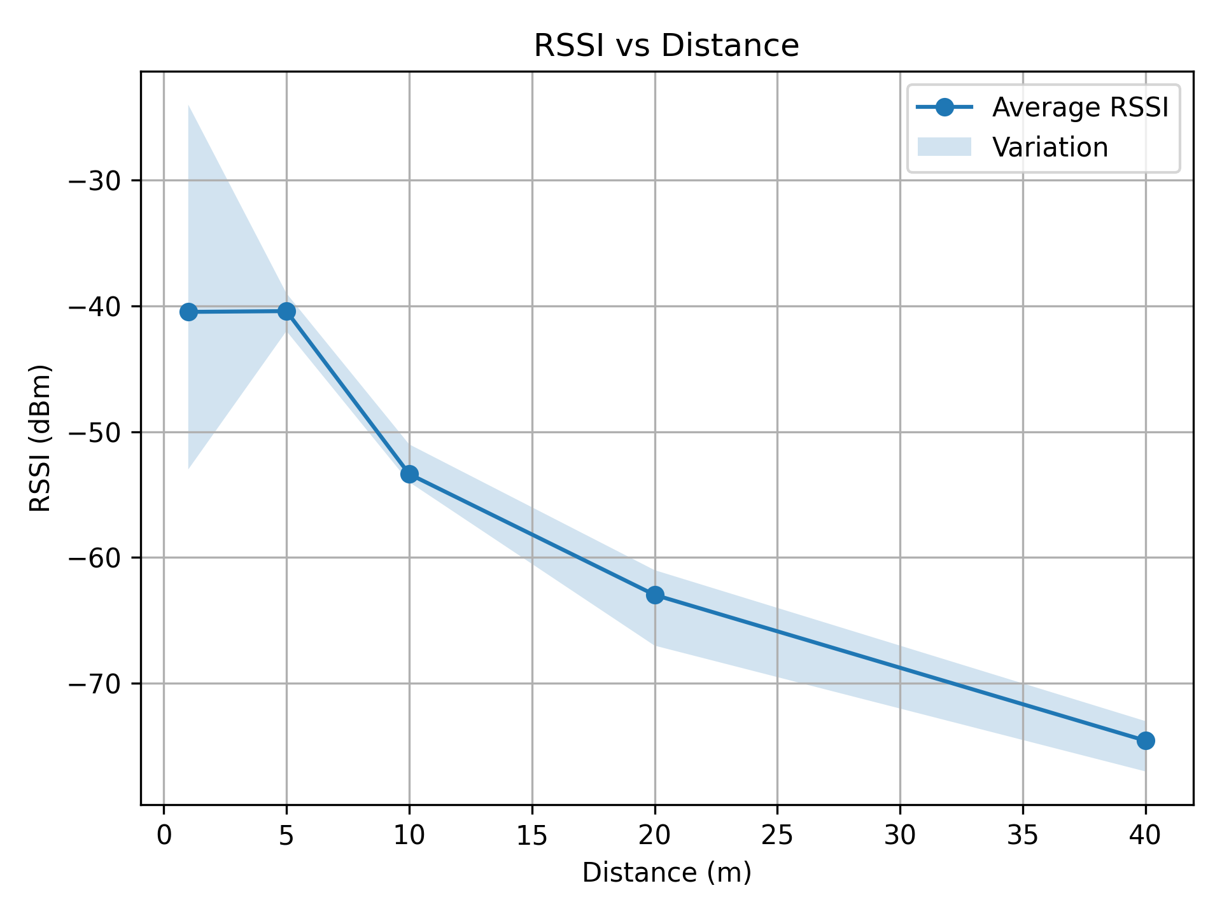
Project tests/RSSI_Antenna_test/rssi_plot_Horizontal_16.9cm_20260521_124703.png
