aGGattack/remoter/Project tests/RSSI_Antenna_test/rssi_plot_Horizontal_17.1cm_20260521_124207.png

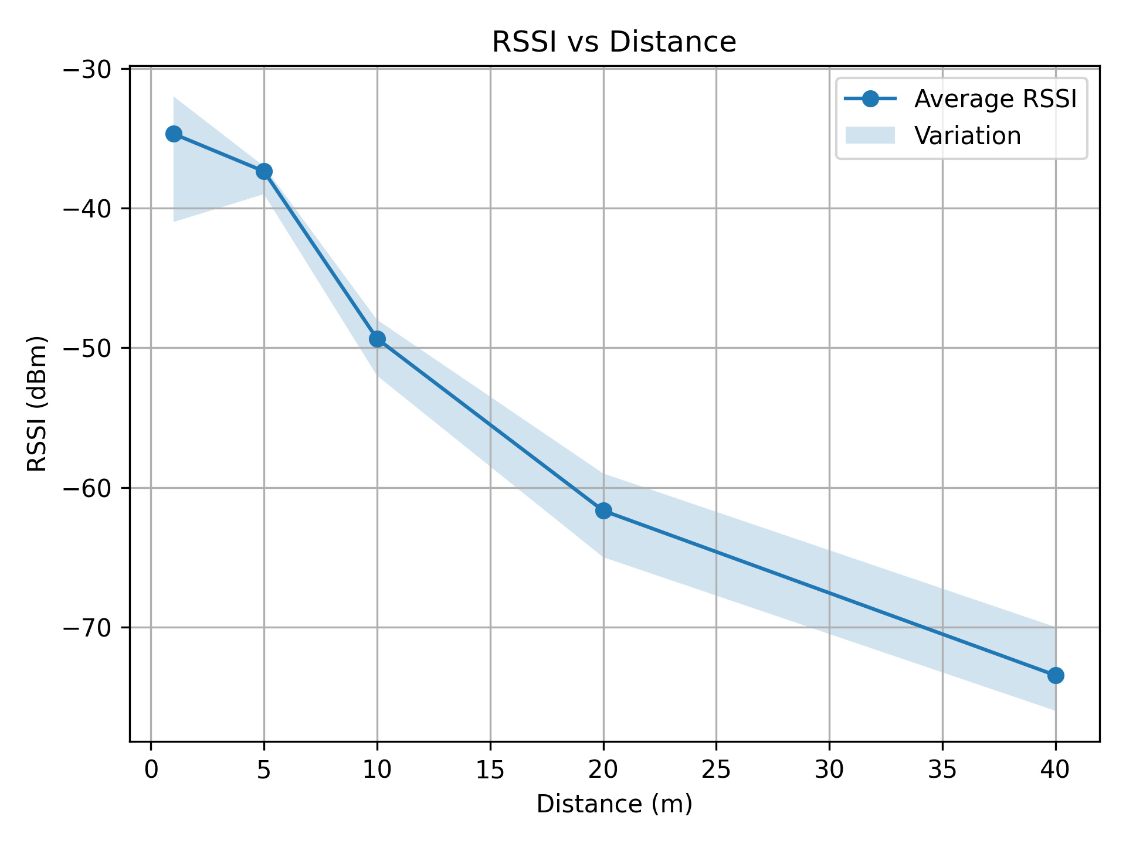
Project tests/RSSI_Antenna_test/rssi_plot_Horizontal_17.1cm_20260521_124207.png
