aGGattack/remoter/Project tests/RSSI_Antenna_test/rssi_plot_Horizontal_17.3cm_20260521_122843.png

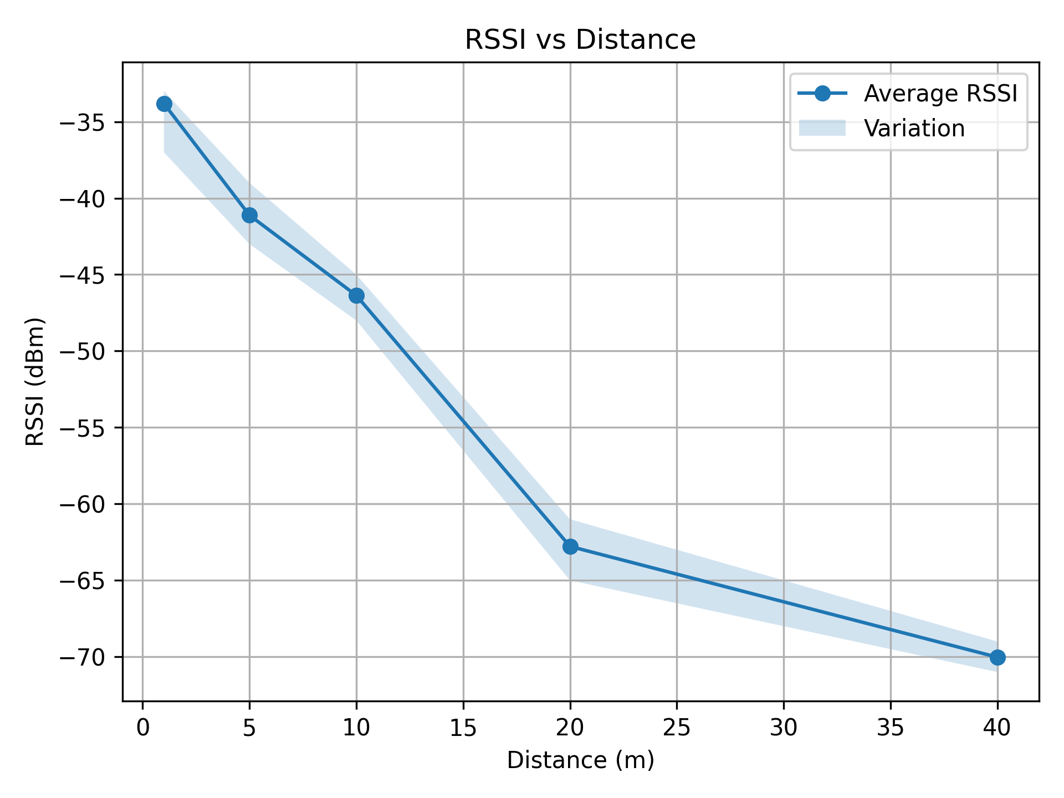
Project tests/RSSI_Antenna_test/rssi_plot_Horizontal_17.3cm_20260521_122843.png
