aGGattack/remoter/Project tests/RSSI_Antenna_test/rssi_plot_Horizontal_18cm_20260521_121640.png

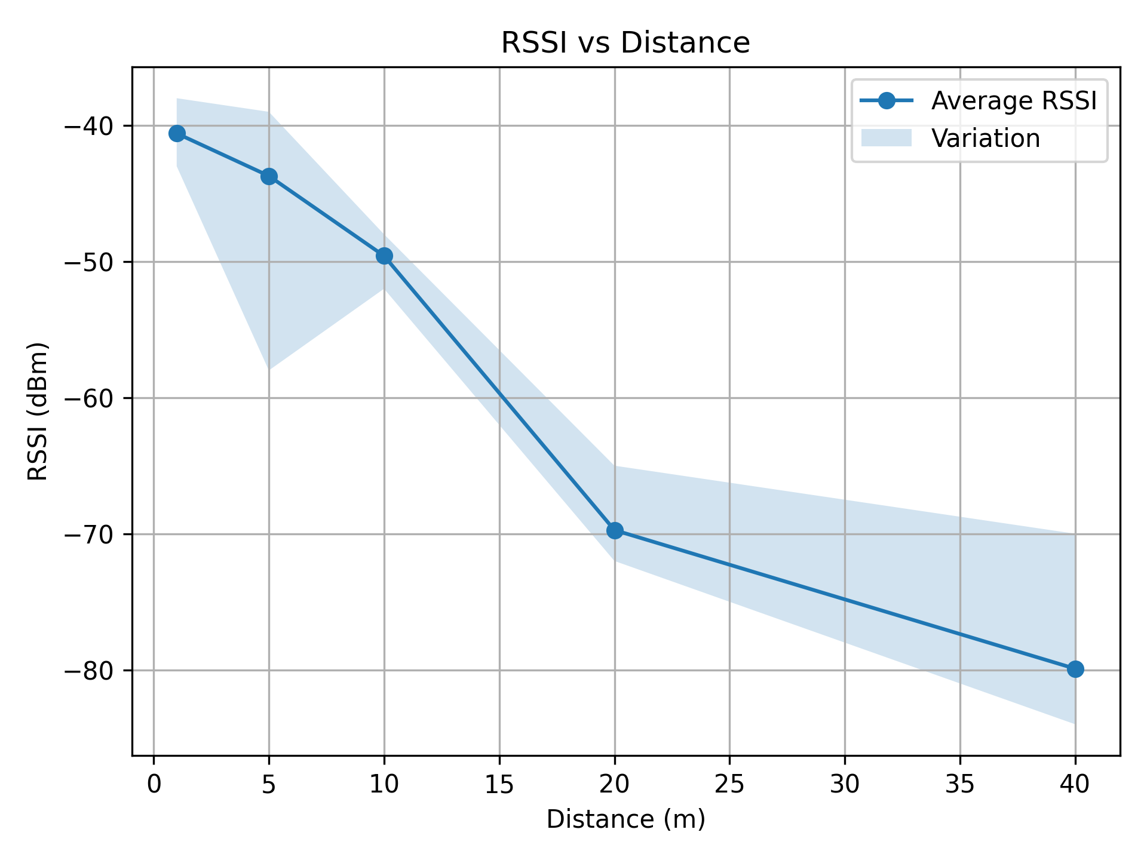
Project tests/RSSI_Antenna_test/rssi_plot_Horizontal_18cm_20260521_121640.png
